gowenrw/future_badge/art/AI_to_DXF.JPG

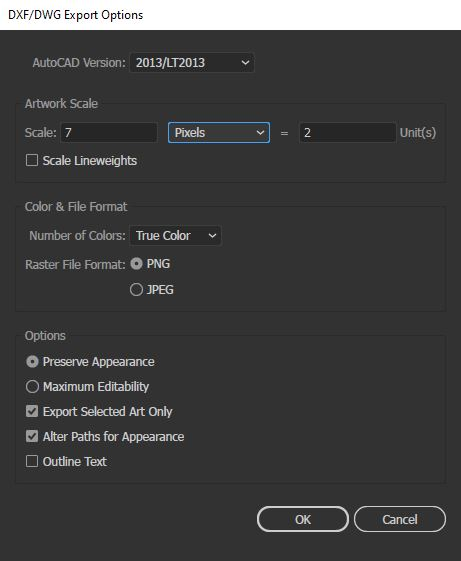
art/AI_to_DXF.JPG
