gowenrw/future_badge/art/haveadrinkonme.jpg

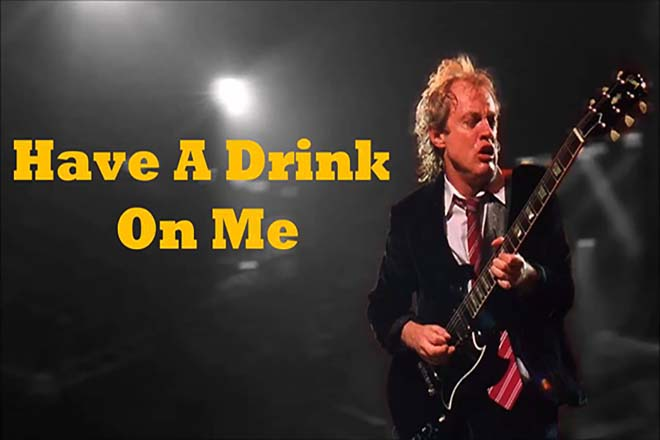
art/haveadrinkonme.jpg
