gowenrw/future_badge/art/inspiration/book_blowing_away.jpg

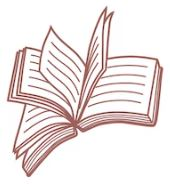
art/inspiration/book_blowing_away.jpg
