gowenrw/future_badge/art/inspiration/book_opening.jpg

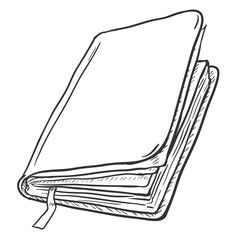
art/inspiration/book_opening.jpg
