gowenrw/future_badge/art/inspiration/bttf_back1.jpg

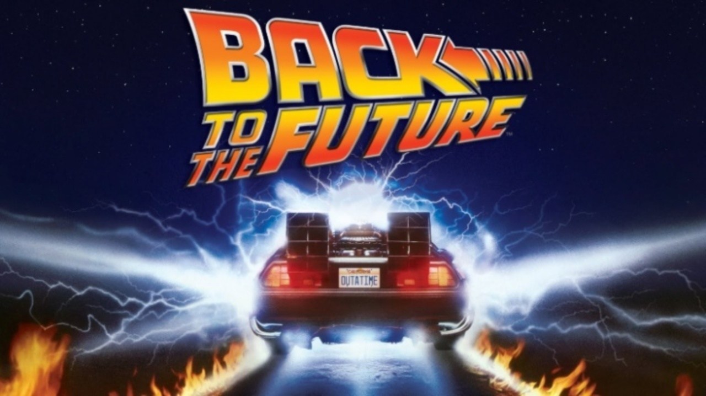
art/inspiration/bttf_back1.jpg
