gowenrw/future_badge/art/inspiration/bttf_back2.jpg

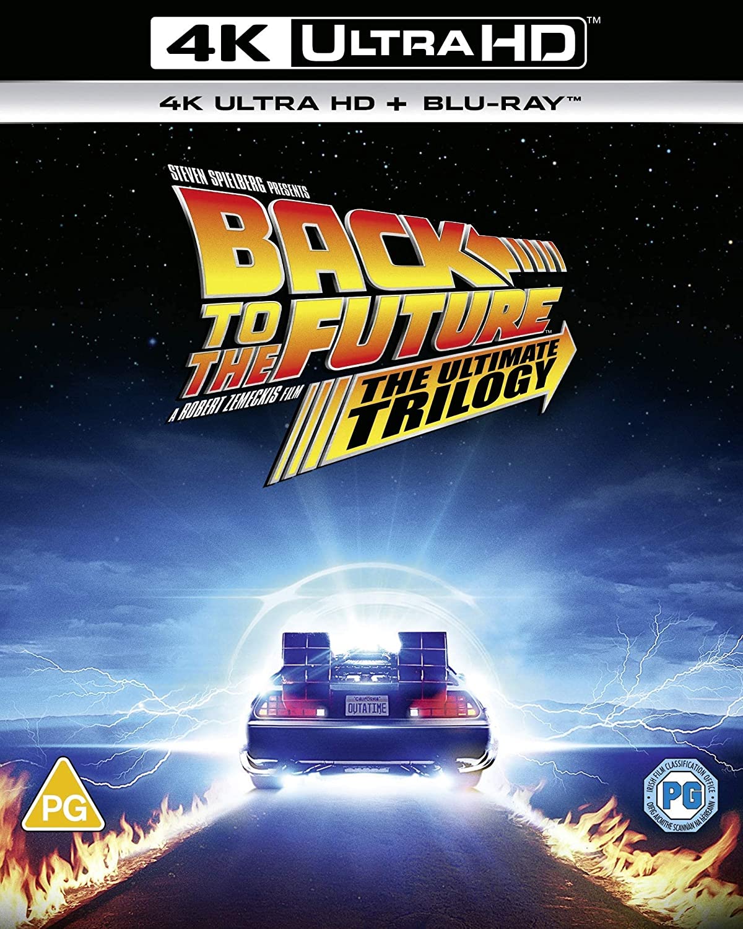
art/inspiration/bttf_back2.jpg
