gowenrw/future_badge/art/inspiration/bttf_side1.jpg

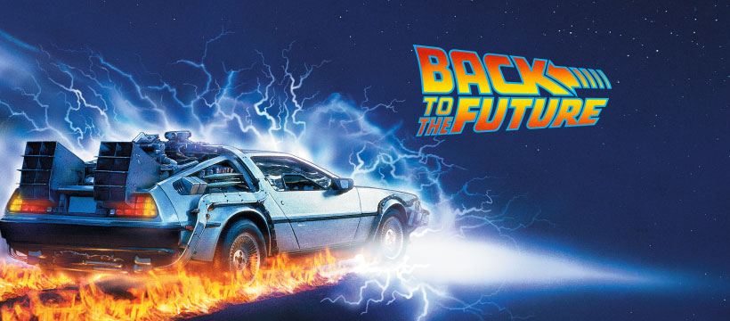
art/inspiration/bttf_side1.jpg
