gowenrw/future_badge/art/inspiration/clock_tower_1.jpg

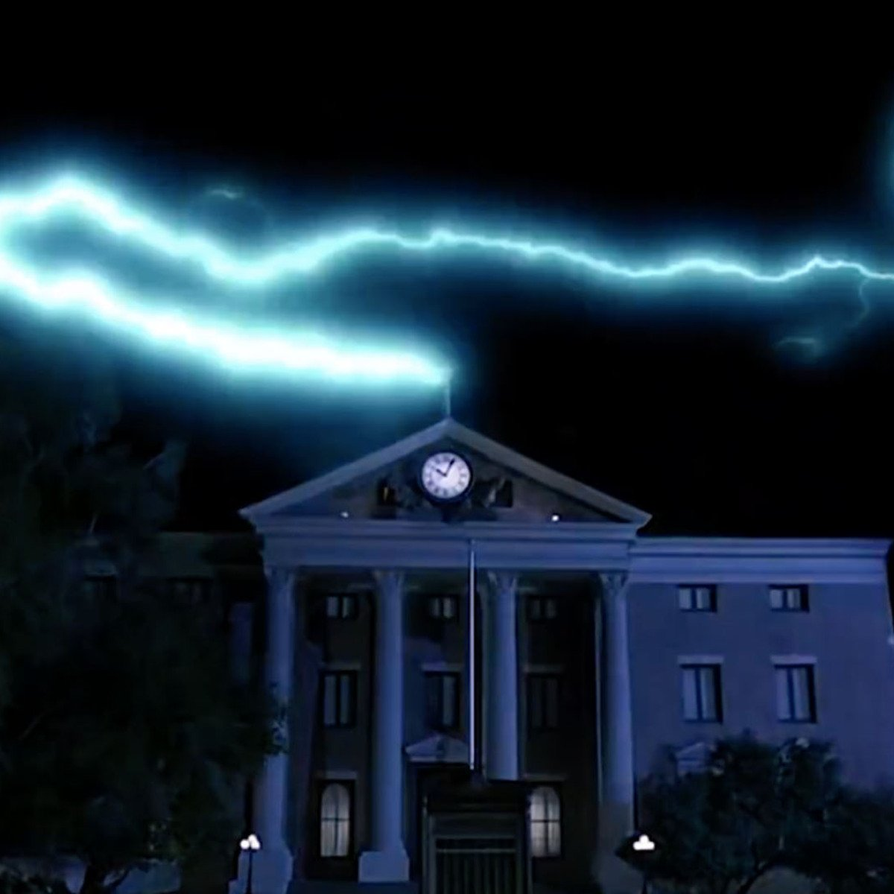
art/inspiration/clock_tower_1.jpg
