gowenrw/future_badge/art/inspiration/Doc-Shock.jpg

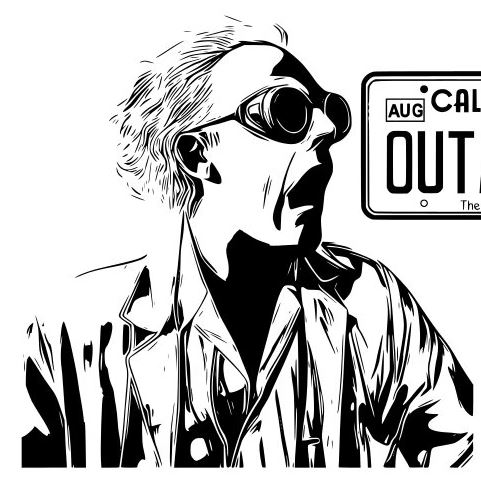
art/inspiration/Doc-Shock.jpg
