gowenrw/future_badge/art/inspiration/flux_cap.jpg

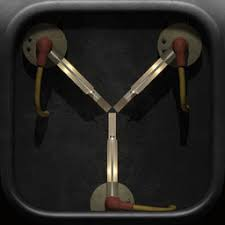
art/inspiration/flux_cap.jpg
