gowenrw/future_badge/art/inspiration/sports_almanac.jpg

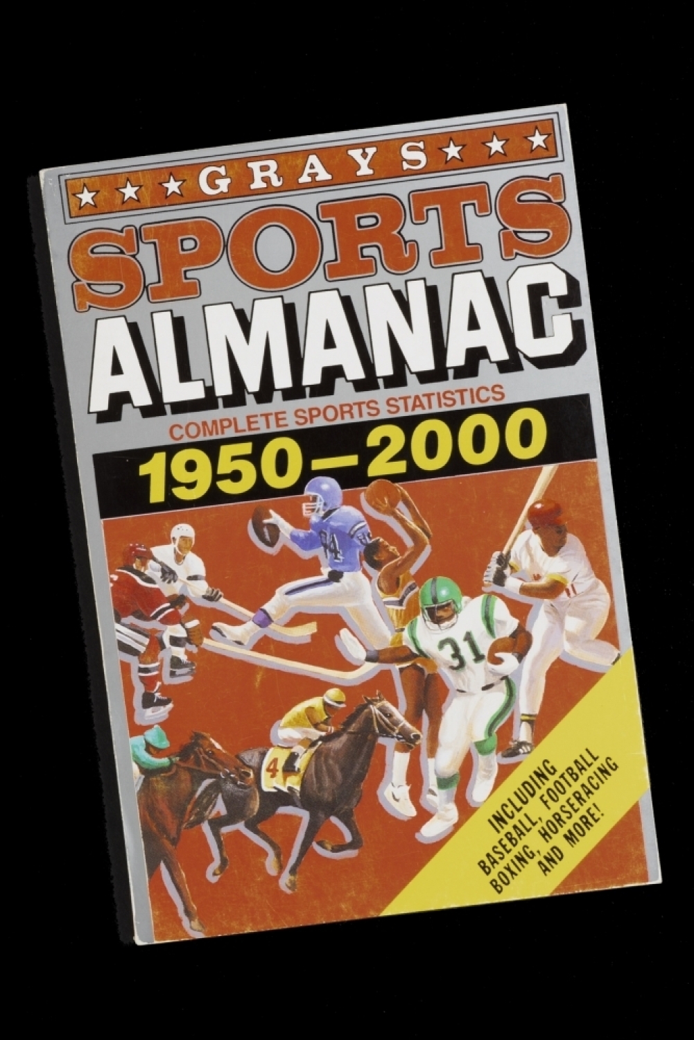
art/inspiration/sports_almanac.jpg
