gowenrw/future_badge/art/lanyard/Proof.png

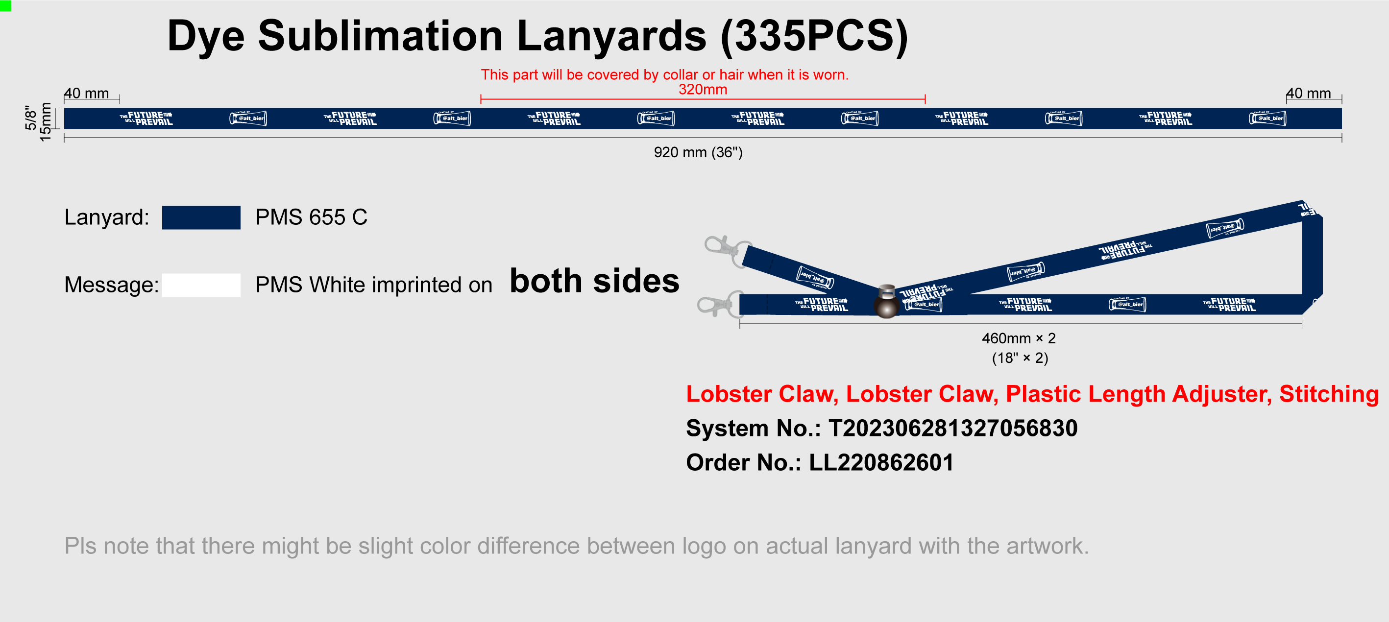
art/lanyard/Proof.png
