gowenrw/future_badge/art/prototype_pcb_full_back.jpg

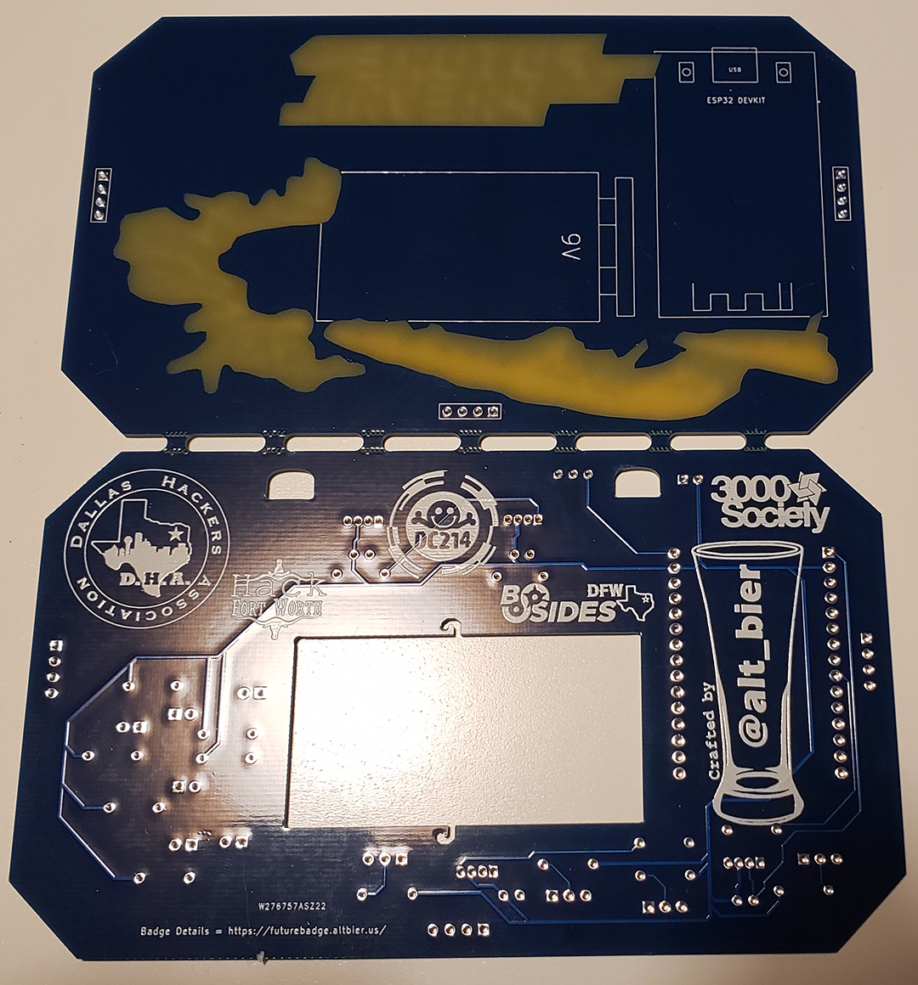
art/prototype_pcb_full_back.jpg
