gowenrw/future_badge/art/prototype_pcb_full_front.jpg

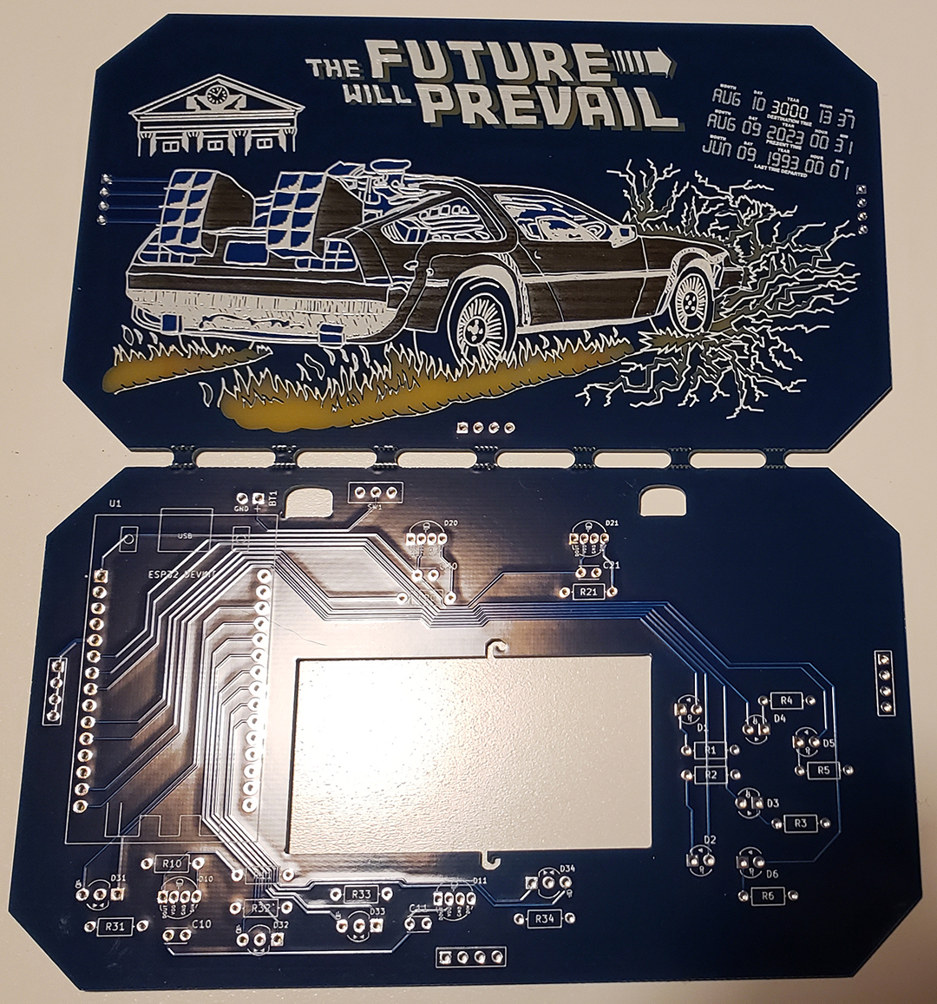
art/prototype_pcb_full_front.jpg
