gowenrw/future_badge/art/prototype_pcb_lit_up.jpg

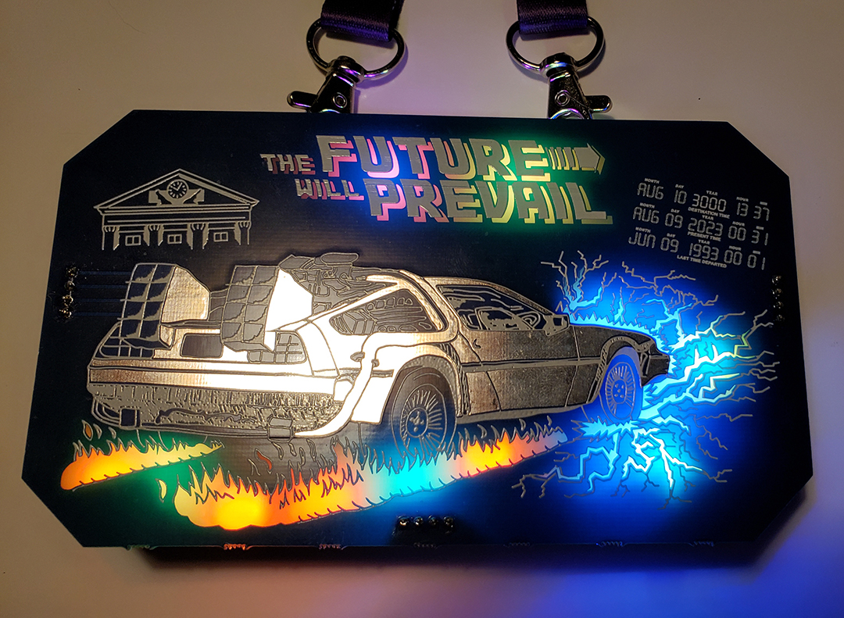
art/prototype_pcb_lit_up.jpg
