gowenrw/future_badge/art/prototype_pcb_lit_up_side_view.jpg

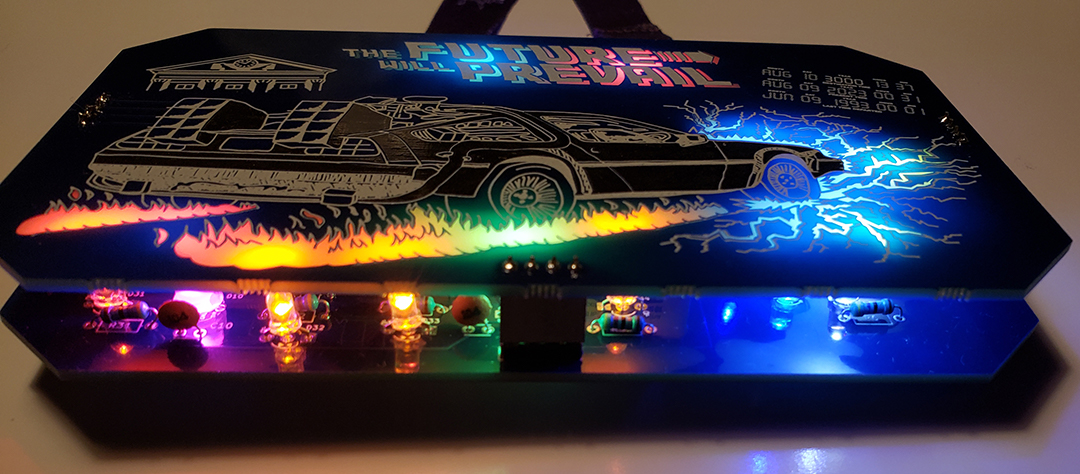
art/prototype_pcb_lit_up_side_view.jpg
