gowenrw/future_badge/art/sticker/Proof_R200018173_StickerMule.png

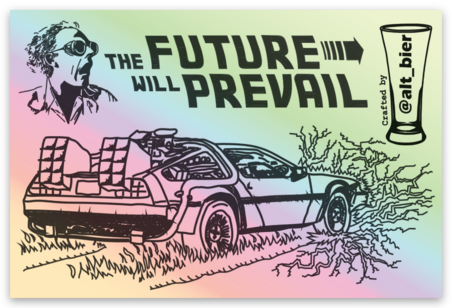
art/sticker/Proof_R200018173_StickerMule.png
