gowenrw/future_badge/docs/images/2Capture.JPG

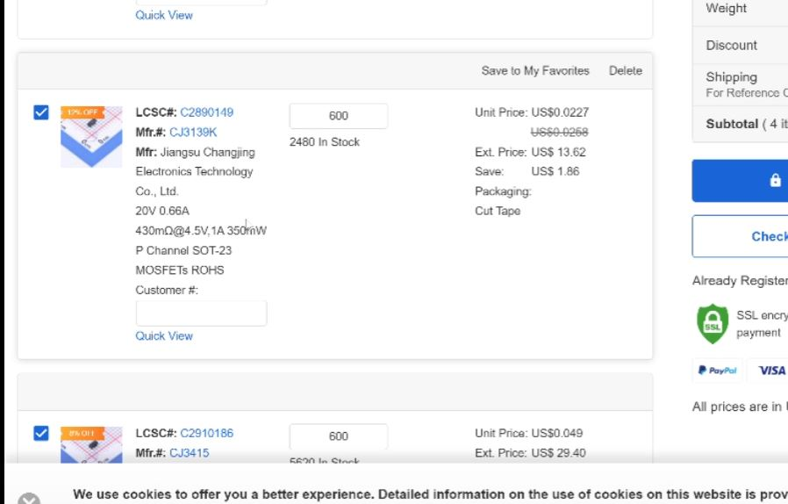
docs/images/2Capture.JPG
