gowenrw/future_badge/docs/images/ESP32-GPIO-Pins-that-are-Safe-to-Use.png

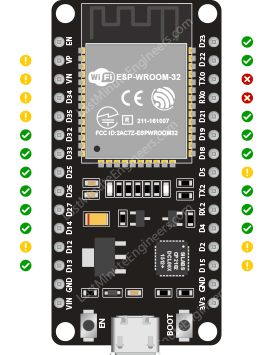
docs/images/ESP32-GPIO-Pins-that-are-Safe-to-Use.png
