gowenrw/future_badge/docs/images/prototype/20230615_201724.jpg

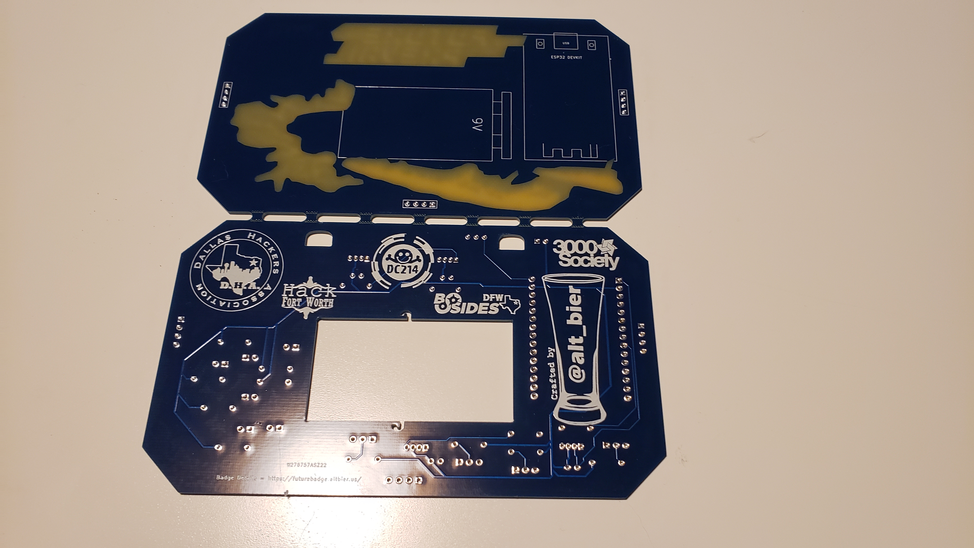
docs/images/prototype/20230615_201724.jpg
