gowenrw/future_badge/docs/images/prototype/20230615_201829.jpg

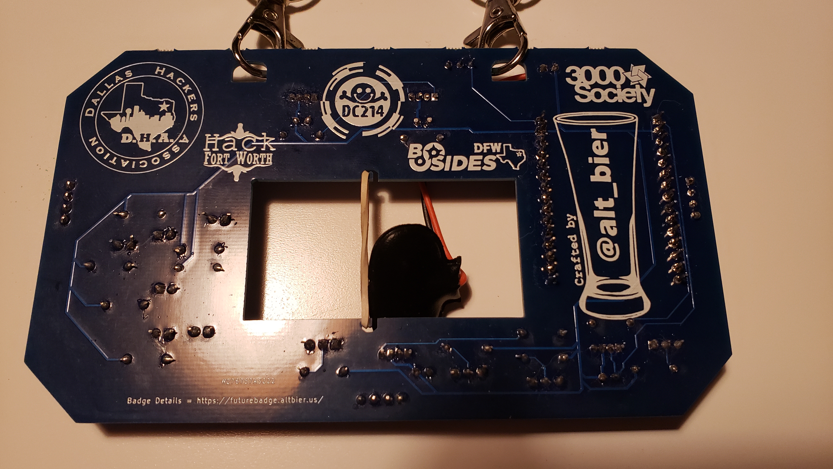
docs/images/prototype/20230615_201829.jpg
