gowenrw/future_badge/docs/images/prototype/20230615_201941.jpg

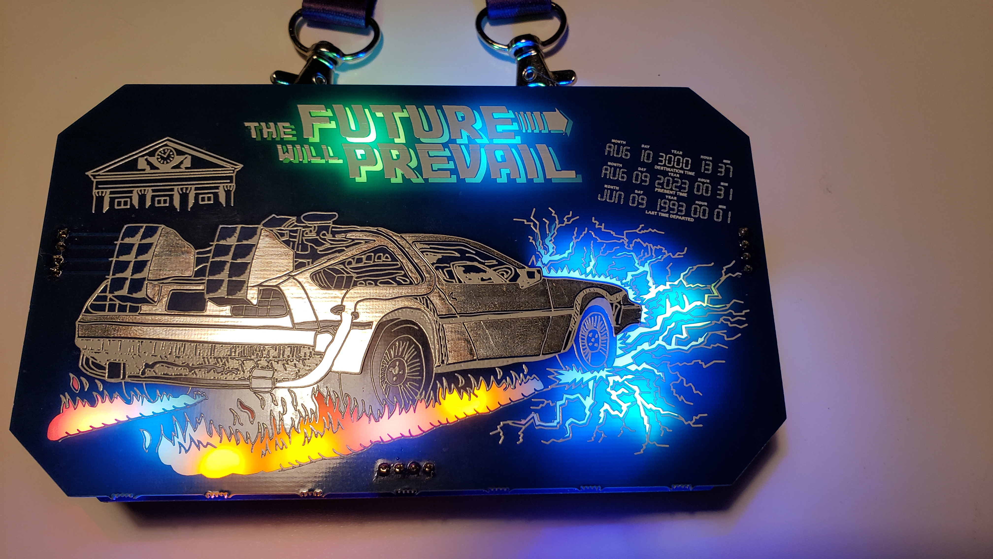
docs/images/prototype/20230615_201941.jpg
