gowenrw/future_badge/docs/images/prototype/20230615_202005.jpg

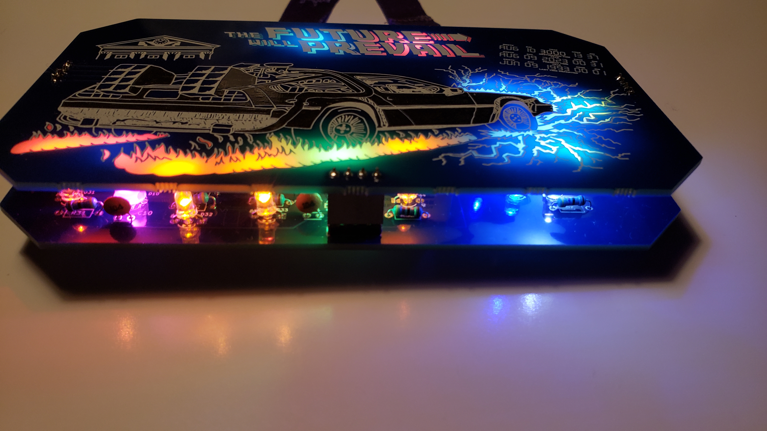
docs/images/prototype/20230615_202005.jpg
