gowenrw/future_badge/docs/images/prototype/20230705_084911.jpg

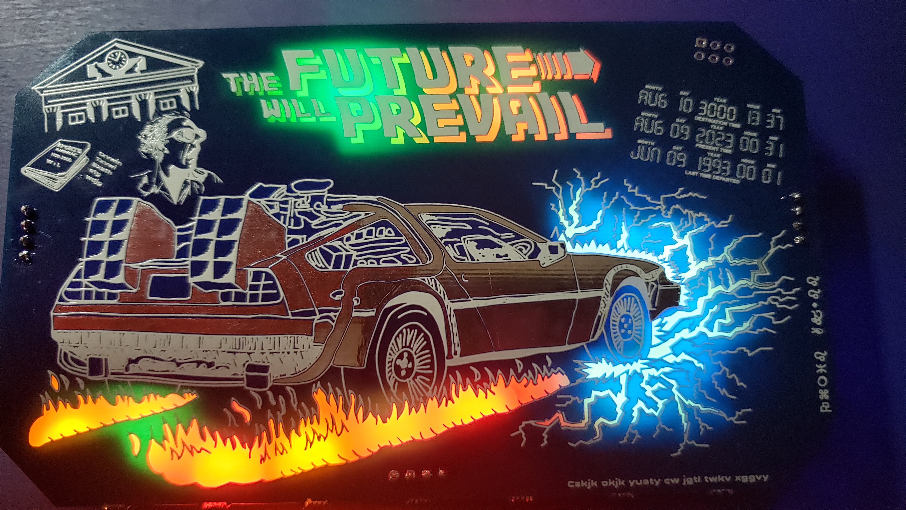
docs/images/prototype/20230705_084911.jpg
