gowenrw/future_badge/docs/images/prototype/20230705_084914.jpg

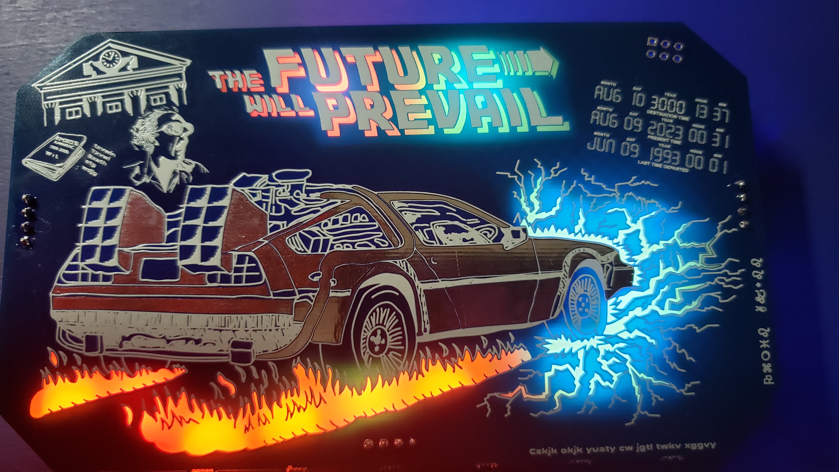
docs/images/prototype/20230705_084914.jpg
