gowenrw/future_badge/docs/images/prototype/20230705_085853.jpg

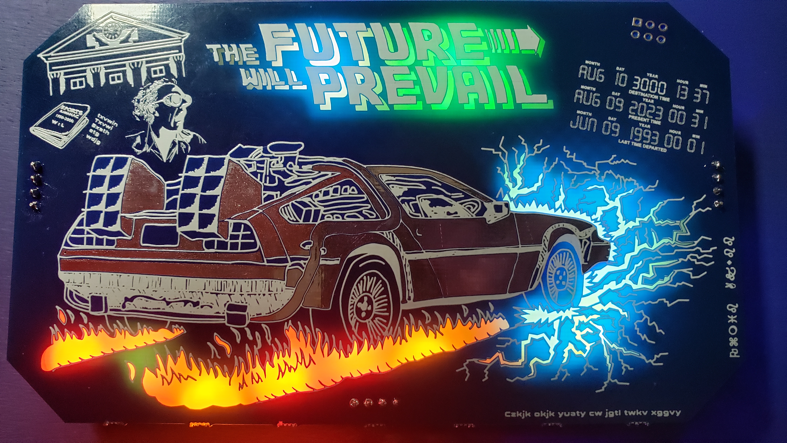
docs/images/prototype/20230705_085853.jpg
