gowenrw/future_badge/art/future_badge_art-2-backmask-lightning-7-2.dxf

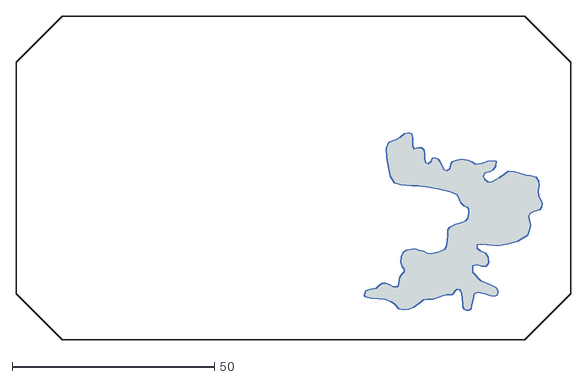
[picture p60: CAD file, 2023-06-05]
art/future_badge_art-2-backmask-lightning-7-2.dxf
137.1 x 80.0
