gowenrw/future_badge/eda/future_badge/3d_models/PinSocket_1x04_P2.54mm_Vertical.step

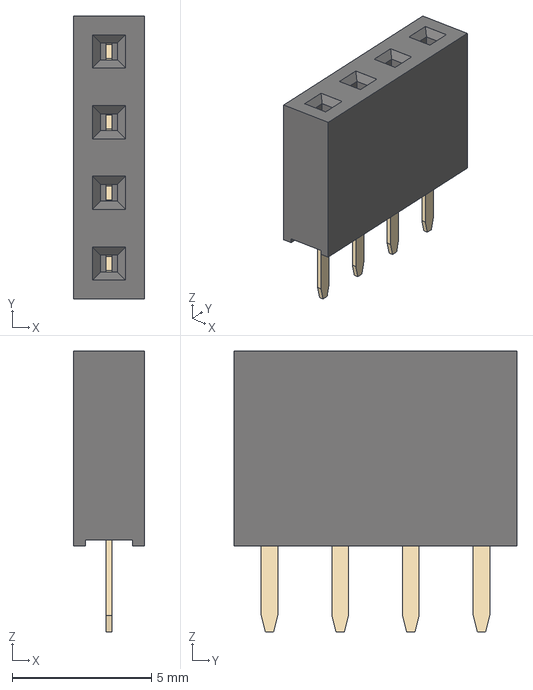
[picture p61: CAD file, 2023-06-05]
eda/future_badge/3d_models/PinSocket_1x04_P2.54mm_Vertical.step
2.54 x 10.2 x 10.1 mm
