gowenrw/future_badge/eda/future_badge/3d_models/PinSocket_1x20_P2.54mm_Vertical.step

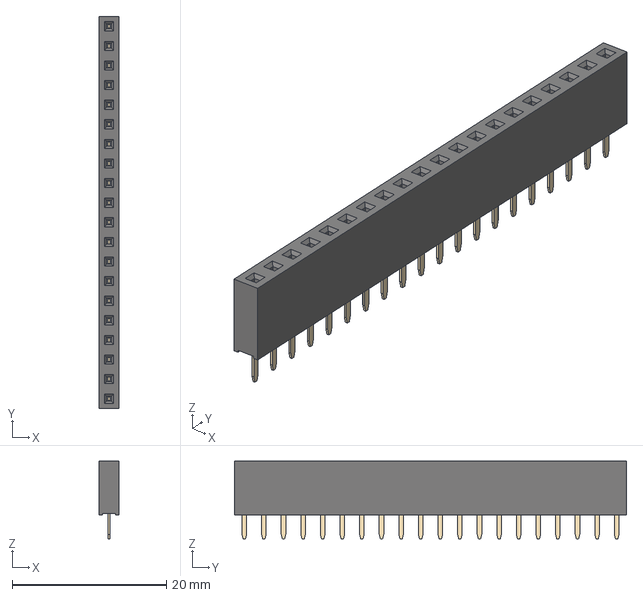
[picture p69: CAD file, 2023-06-05]
eda/future_badge/3d_models/PinSocket_1x20_P2.54mm_Vertical.step
2.54 x 50.8 x 10.1 mm
