gowenrw/future_badge/art/future_badge_art-2-frontsilk-title-txt-7-2.dxf

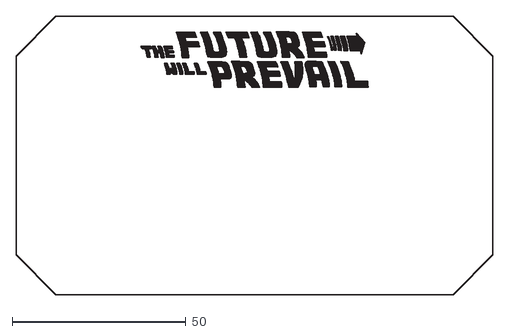
[picture p70: CAD file, 2023-06-03]
art/future_badge_art-2-frontsilk-title-txt-7-2.dxf
137.1 x 80.0
