gowenrw/future_badge/art/future_badge_art-2-frontsilk-notxt-7-2.dxf

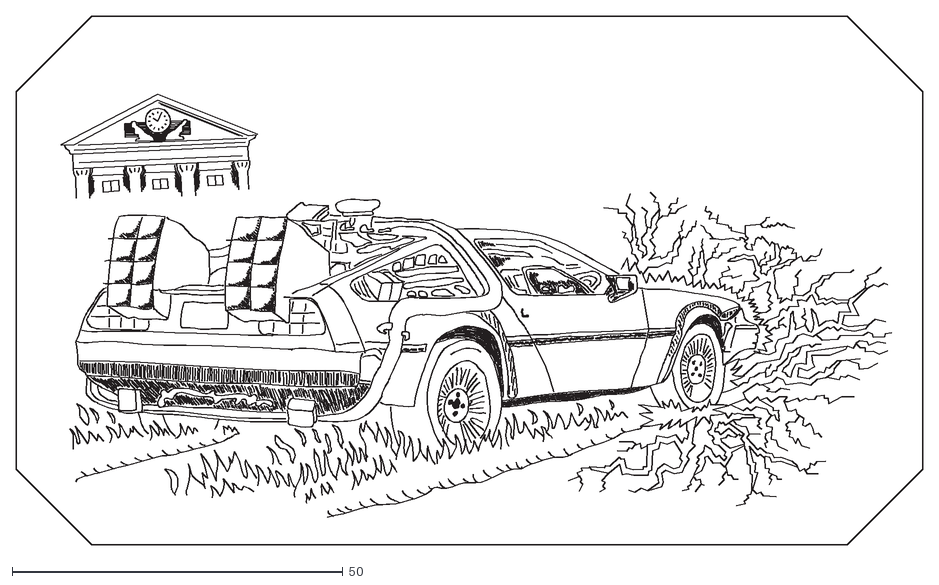
[picture p72: CAD file, 2023-06-03]
art/future_badge_art-2-frontsilk-notxt-7-2.dxf
137.1 x 80.0
