gowenrw/future_badge/art/future_badge_art-2-edgecuts-7-2.dxf

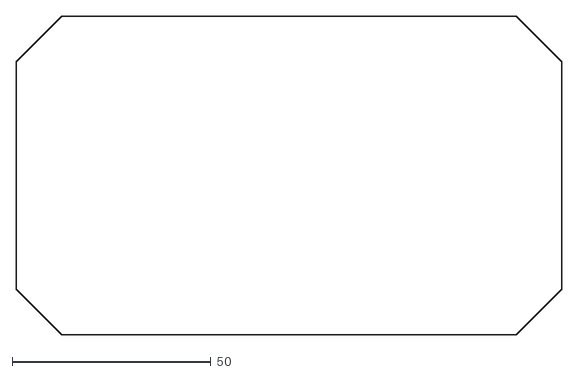
[picture p76: CAD file, 2023-06-03]
art/future_badge_art-2-edgecuts-7-2.dxf
137.1 x 80.0
