gowenrw/future_badge/eda/future_badge/3d_models/PinSocket_1x03_P2.54mm_Horizontal.step

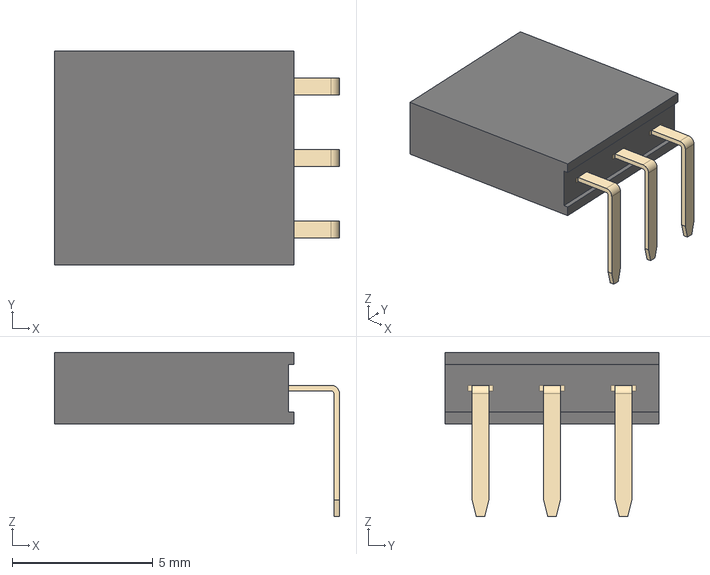
[picture p77: CAD file, 2023-06-05]
eda/future_badge/3d_models/PinSocket_1x03_P2.54mm_Horizontal.step
10.1 x 7.62 x 5.84 mm
