gowenrw/future_badge/eda/future_badge/3d_models/PinSocket_1x04_P2.54mm_Horizontal.step

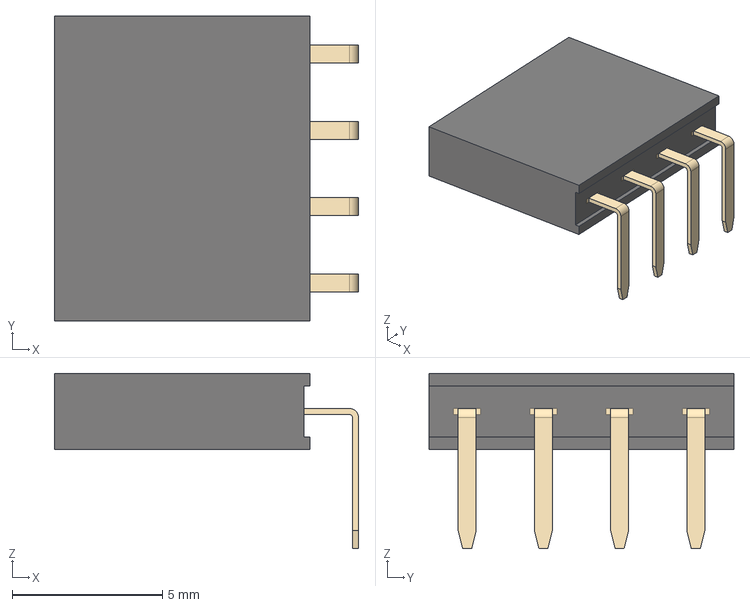
[picture p79: CAD file, 2023-06-05]
eda/future_badge/3d_models/PinSocket_1x04_P2.54mm_Horizontal.step
10.1 x 10.2 x 5.84 mm
