gowenrw/future_badge/eda/future_badge/3d_models/LED_D5.0mm-4_RGB_Neo.step

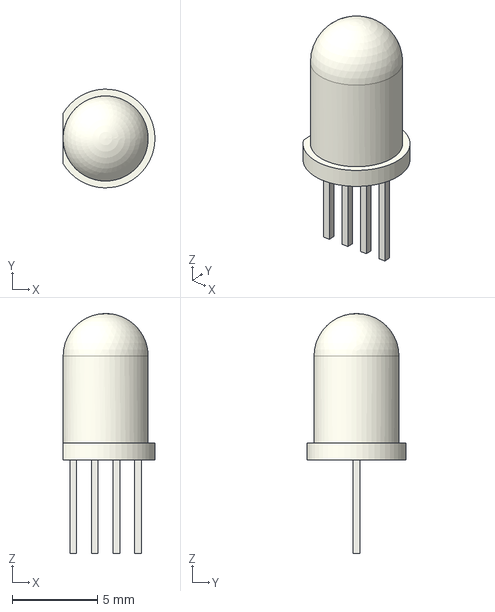
[picture p81: CAD file, 2023-04-15]
eda/future_badge/3d_models/LED_D5.0mm-4_RGB_Neo.step
5.40 x 5.79 x 14.1 mm
