gowenrw/future_badge/eda/future_badge/3d_models/USB_Micro-B_Molex_47346-0001.step

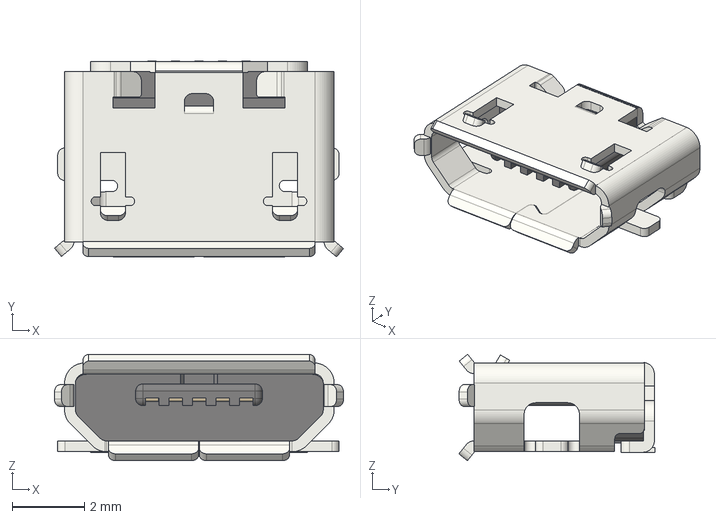
[picture p82: CAD file, 2023-04-15]
eda/future_badge/3d_models/USB_Micro-B_Molex_47346-0001.step
7.98 x 5.42 x 2.94 mm
