gowenrw/future_badge/eda/future_badge/3d_models/CP_Radial_D6.3mm_P2.50mm.step

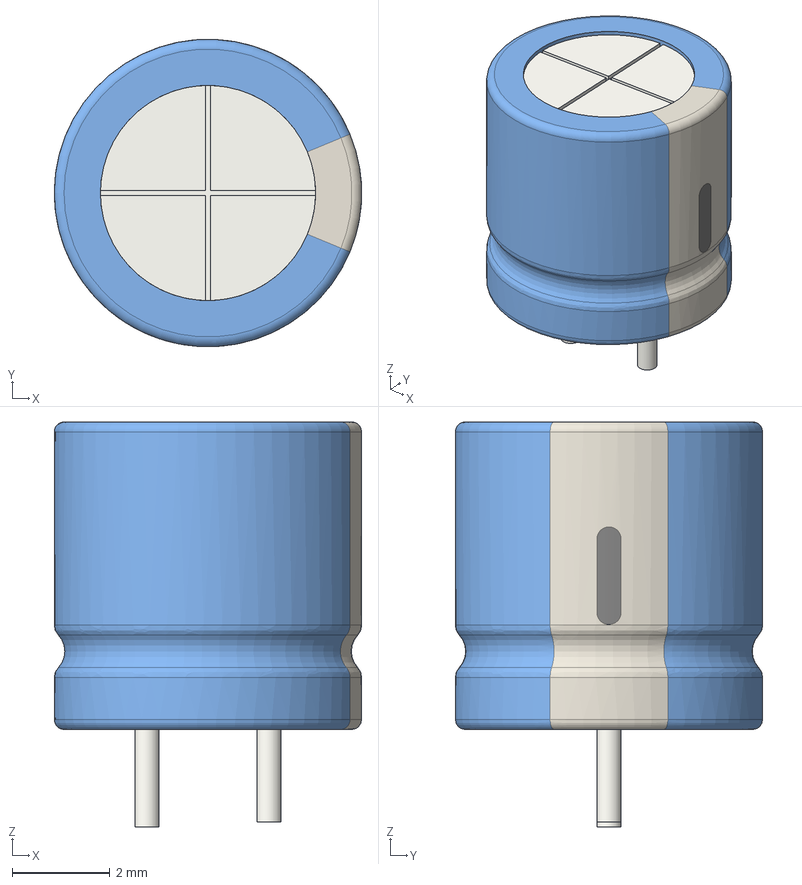
[picture p83: CAD file, 2023-04-15]
eda/future_badge/3d_models/CP_Radial_D6.3mm_P2.50mm.step
6.30 x 6.30 x 8.30 mm
