gowenrw/future_badge/eda/future_badge/3d_models/PinHeader_1x06_P2.54mm_Horizontal.step

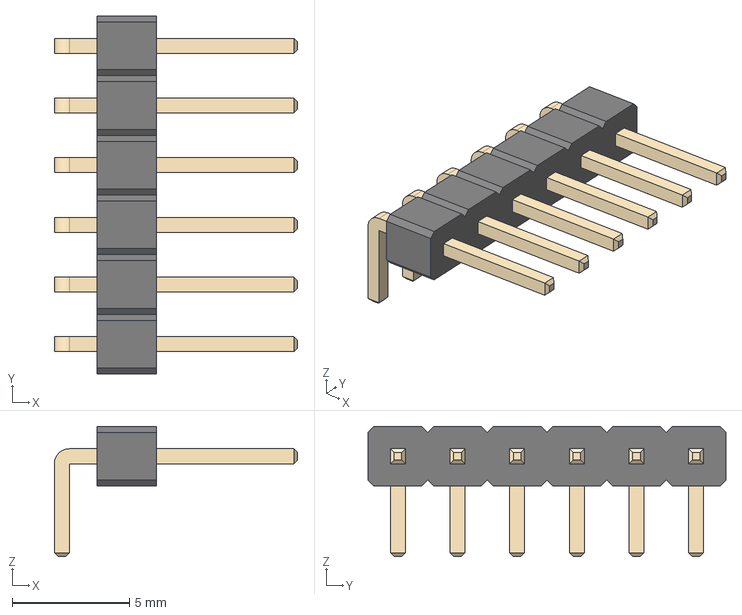
[picture p89: CAD file, 2023-04-15]
eda/future_badge/3d_models/PinHeader_1x06_P2.54mm_Horizontal.step
10.4 x 15.2 x 5.54 mm
