gowenrw/future_badge/eda/future_badge/3d_models/PinSocket_1x01_P2.54mm_Vertical.step

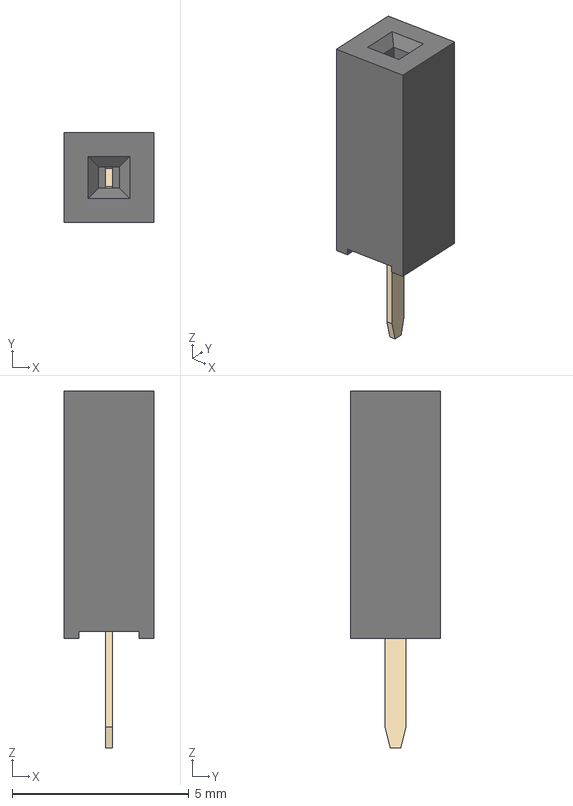
[picture p92: CAD file, 2023-04-15]
eda/future_badge/3d_models/PinSocket_1x01_P2.54mm_Vertical.step
2.54 x 2.54 x 10.1 mm
