gowenrw/future_badge/eda/future_badge/3d_models/PinSocket_1x08_P2.54mm_Horizontal.step

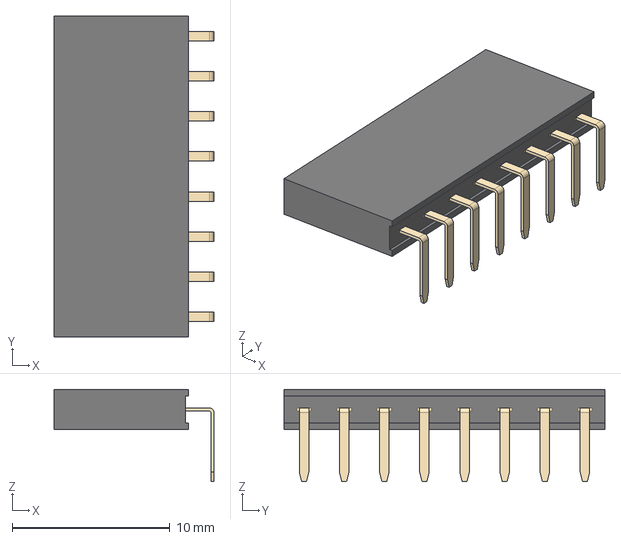
[picture p93: CAD file, 2023-04-15]
eda/future_badge/3d_models/PinSocket_1x08_P2.54mm_Horizontal.step
10.1 x 20.3 x 5.84 mm
