gowenrw/future_badge/eda/future_badge/3d_models/Battery_Holder_3xAAA_Simple.step

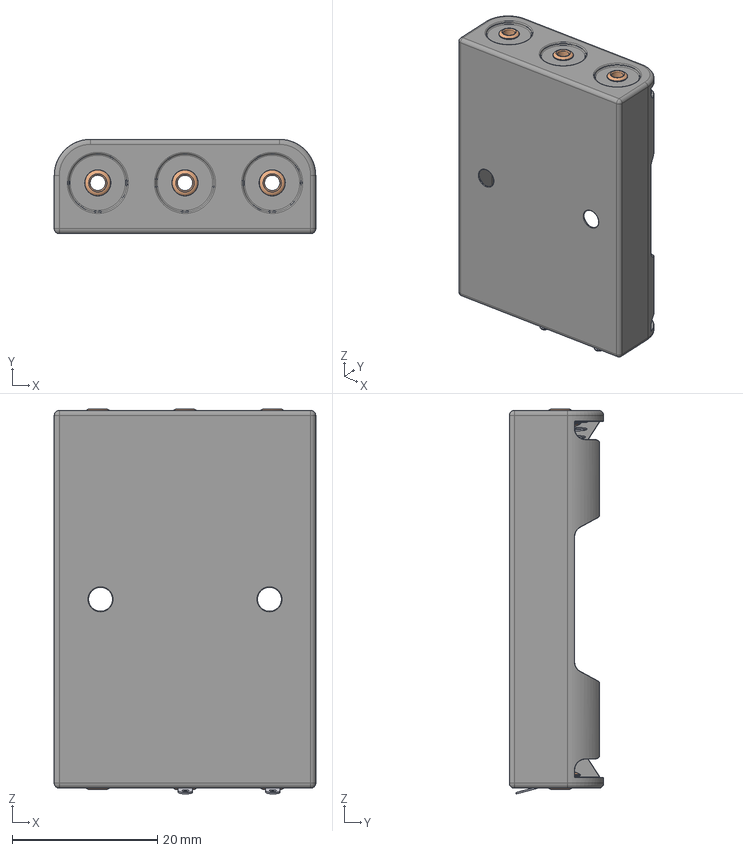
[picture p94: CAD file, 2023-04-15]
eda/future_badge/3d_models/Battery_Holder_3xAAA_Simple.step
36.0 x 13.0 x 53.0 mm
