gowenrw/future_badge/eda/future_badge/3d_models/LED_0805_2012Metric_Castellated.step

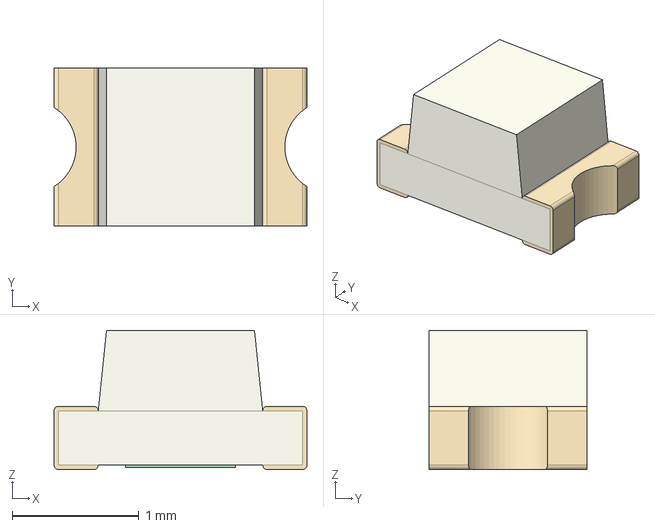
[picture p97: CAD file, 2023-04-15]
eda/future_badge/3d_models/LED_0805_2012Metric_Castellated.step
2.00 x 1.25 x 1.10 mm
