gowenrw/future_badge/eda/future_badge/3d_models/LED_D8.0mm.step

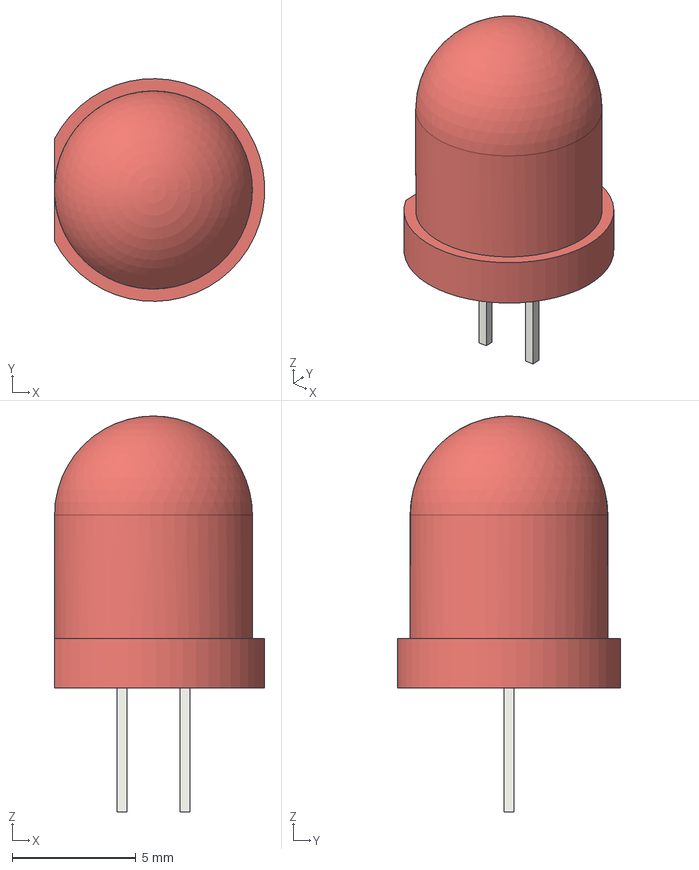
[picture p98: CAD file, 2023-04-15]
eda/future_badge/3d_models/LED_D8.0mm.step
8.49 x 9.00 x 16.0 mm
