gowenrw/future_badge/eda/future_badge/3d_models/PinHeader_1x04_P2.54mm_Vertical.step

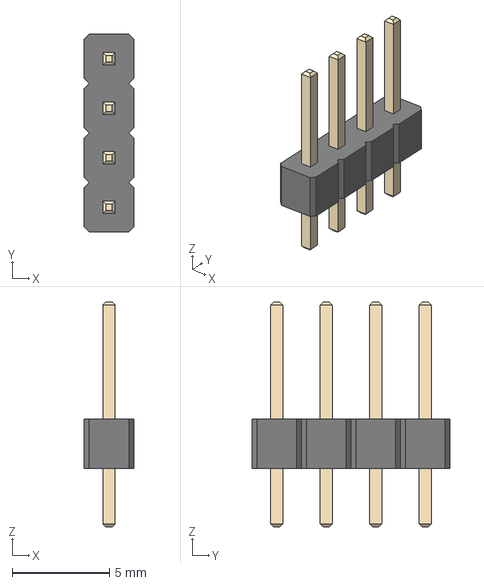
[picture p100: CAD file, 2023-04-15]
eda/future_badge/3d_models/PinHeader_1x04_P2.54mm_Vertical.step
2.54 x 10.2 x 11.5 mm
