gowenrw/future_badge/eda/future_badge/3d_models/LED_D5.0mm.step

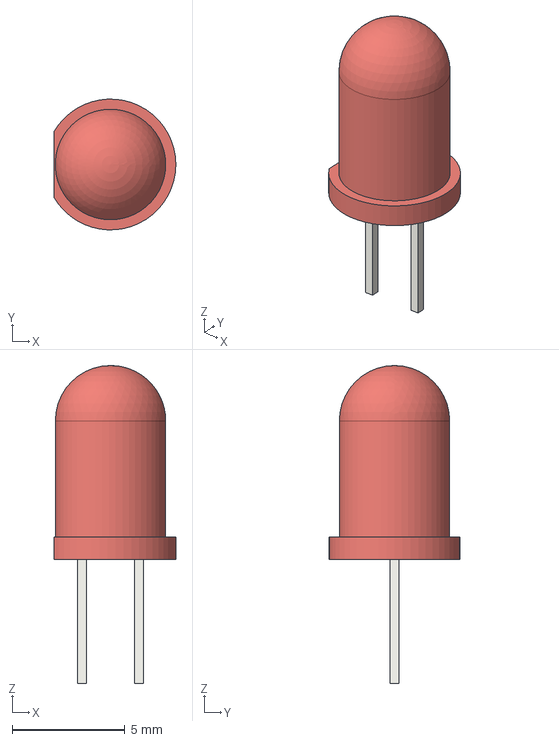
[picture p101: CAD file, 2023-04-15]
eda/future_badge/3d_models/LED_D5.0mm.step
5.40 x 5.79 x 14.1 mm
