gowenrw/future_badge/eda/future_badge/3d_models/BatteryHolder_2466_1xAAA.step

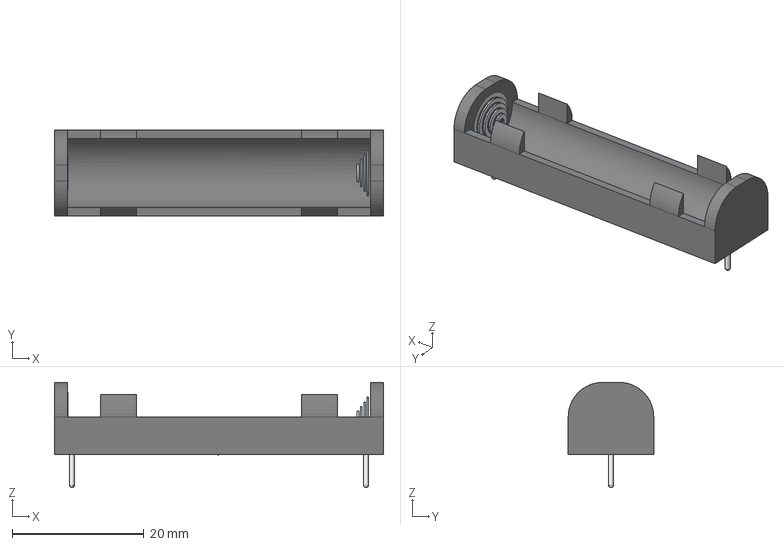
[picture p102: CAD file, 2023-04-15]
eda/future_badge/3d_models/BatteryHolder_2466_1xAAA.step
50.0 x 13.0 x 16.0 mm
