gowenrw/future_badge/eda/future_badge/3d_models/RJ45_Amphenol_RJHSE538X.step

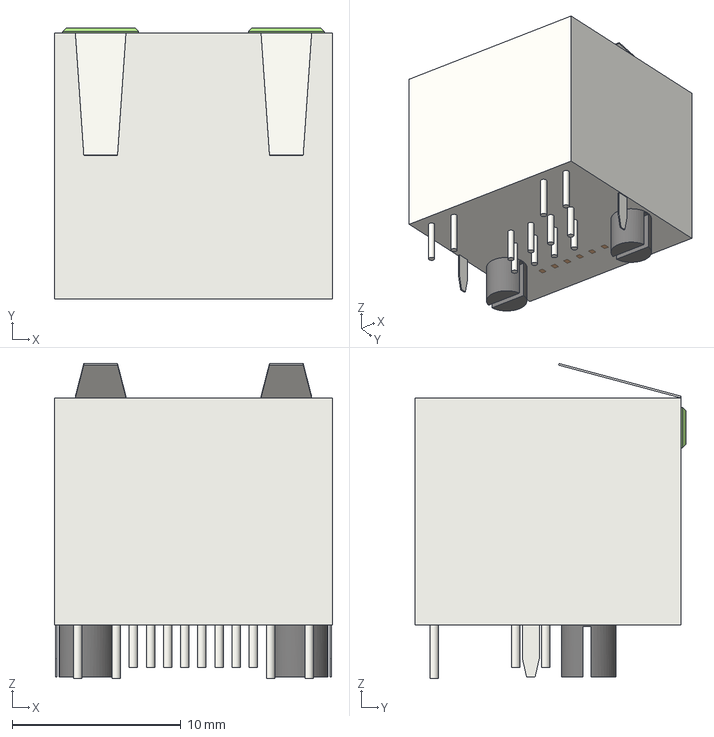
[picture p103: CAD file, 2023-04-15]
eda/future_badge/3d_models/RJ45_Amphenol_RJHSE538X.step
16.5 x 16.1 x 18.7 mm
