gowenrw/future_badge/eda/future_badge/3d_models/R_0805_2012Metric.step

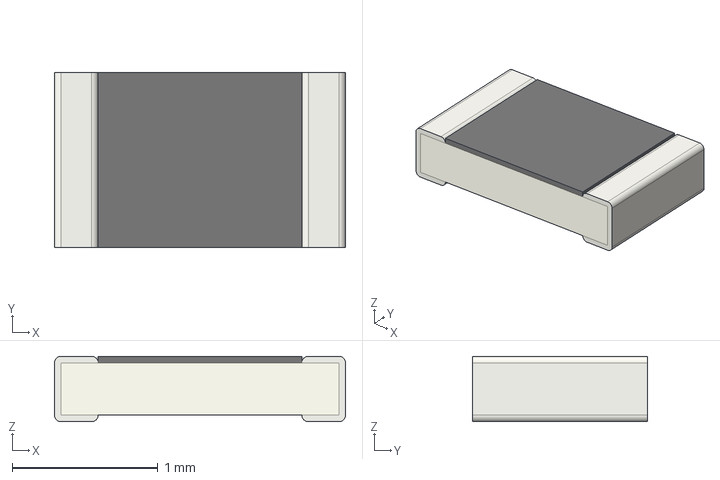
[picture p105: CAD file, 2023-04-15]
eda/future_badge/3d_models/R_0805_2012Metric.step
2.00 x 1.20 x 0.45 mm
