gowenrw/future_badge/eda/future_badge/3d_models/Battery_Holder_CR2032_BS-2-1.stp

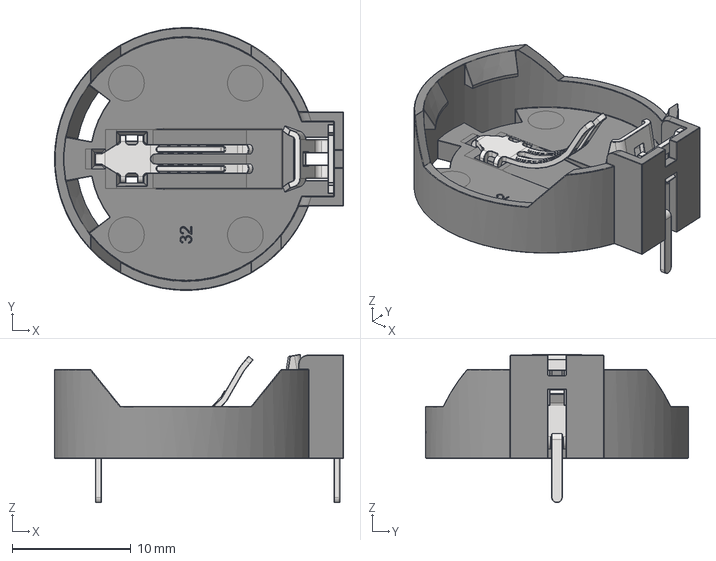
[picture p106: CAD file, 2023-04-15]
eda/future_badge/3d_models/Battery_Holder_CR2032_BS-2-1.stp
24.3 x 22.1 x 12.5 mm
