gowenrw/future_badge/eda/future_badge/3d_models/C_1206_3216Metric.step

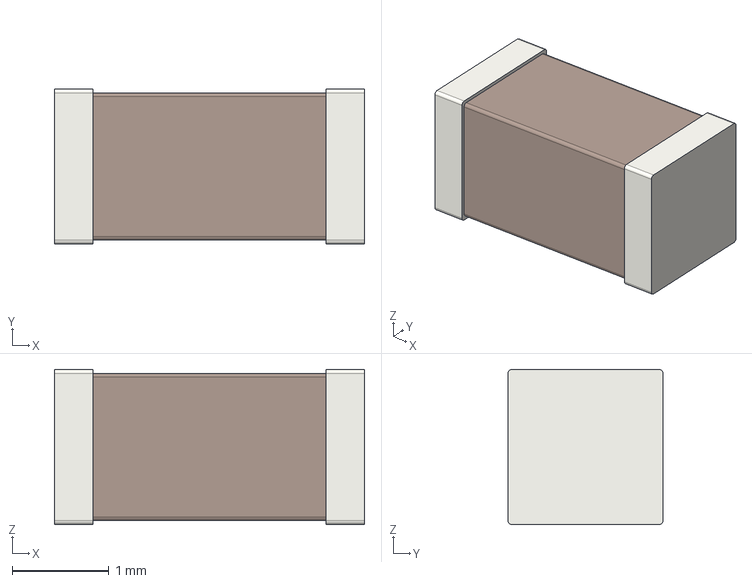
[picture p107: CAD file, 2023-04-15]
eda/future_badge/3d_models/C_1206_3216Metric.step
3.20 x 1.60 x 1.60 mm
