gowenrw/future_badge/eda/future_badge/3d_models/LED_D3.0mm-3.step

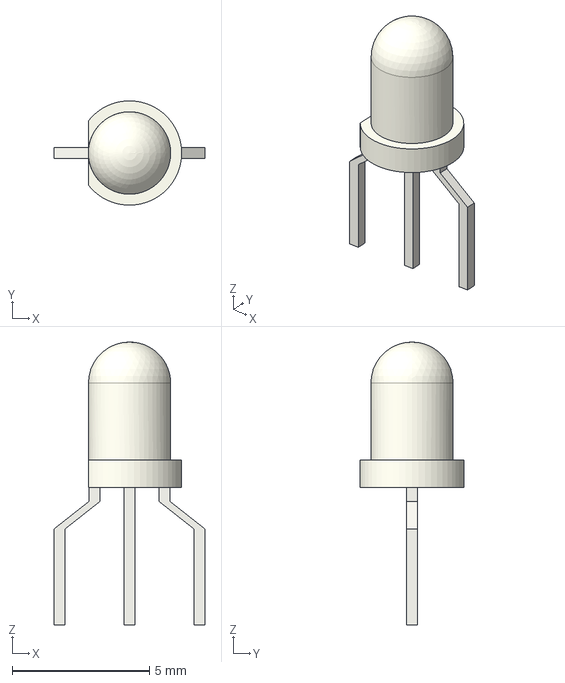
[picture p108: CAD file, 2023-04-15]
eda/future_badge/3d_models/LED_D3.0mm-3.step
5.48 x 3.80 x 10.3 mm
