gowenrw/future_badge/eda/future_badge/3d_models/R_0603_1608Metric.step

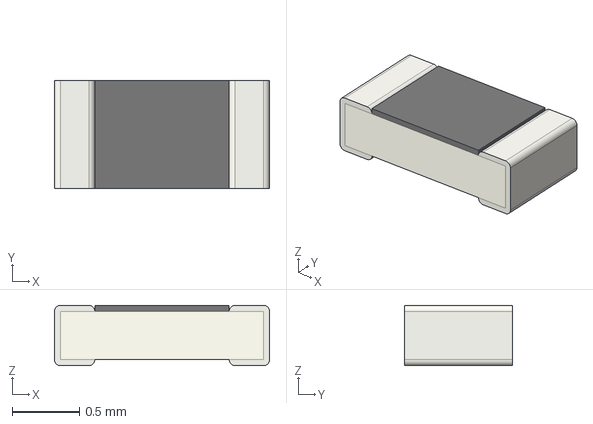
[picture p109: CAD file, 2023-04-15]
eda/future_badge/3d_models/R_0603_1608Metric.step
1.60 x 0.8 x 0.45 mm
