gowenrw/future_badge/eda/future_badge/3d_models/LED_0603_1608Metric_Castellated.step

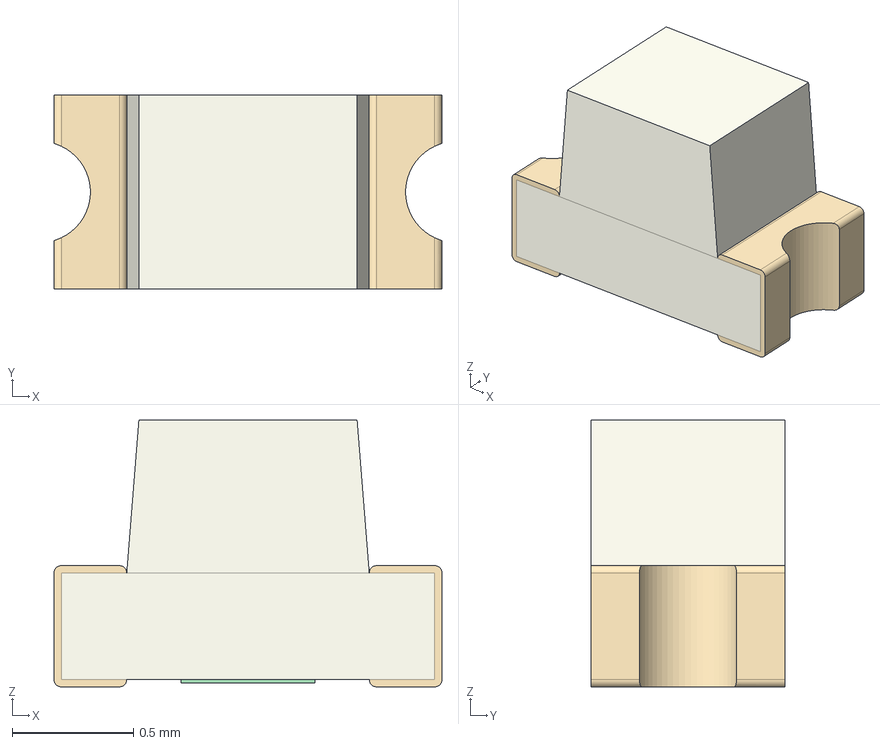
[picture p113: CAD file, 2023-04-15]
eda/future_badge/3d_models/LED_0603_1608Metric_Castellated.step
1.60 x 0.8 x 1.10 mm
