gowenrw/future_badge/eda/future_badge/3d_models/SW_SPDT_PCM12.step

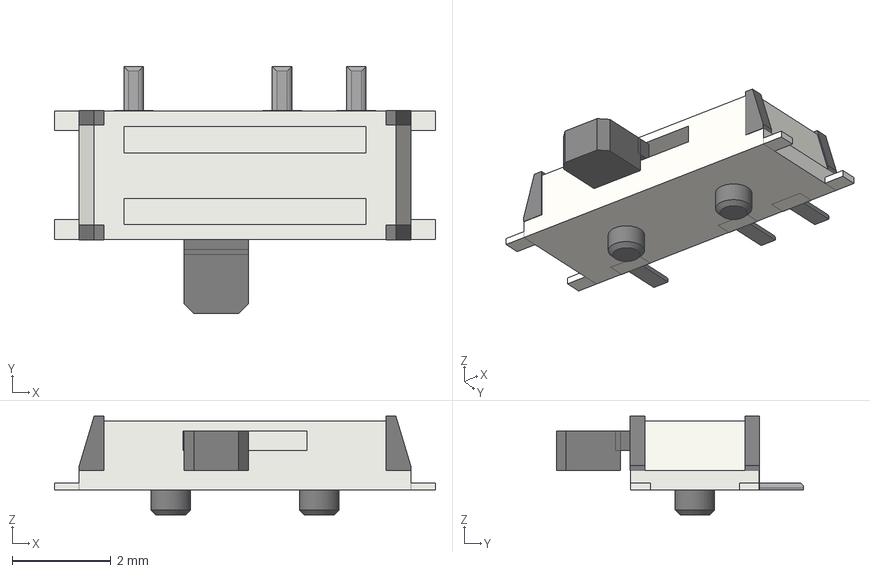
[picture p114: CAD file, 2023-04-15]
eda/future_badge/3d_models/SW_SPDT_PCM12.step
7.70 x 5.00 x 2.00 mm
