gowenrw/future_badge/eda/future_badge/3d_models/TS2306A.step

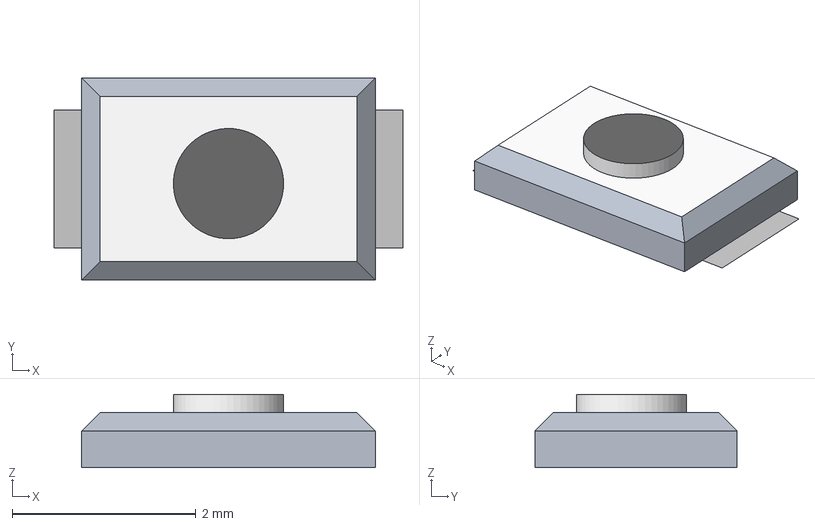
[picture p116: CAD file, 2023-04-15]
eda/future_badge/3d_models/TS2306A.step
3.80 x 2.20 x 0.8 mm
Plane
