gowenrw/future_badge/eda/future_badge/3d_models/C_0805_2012Metric.step

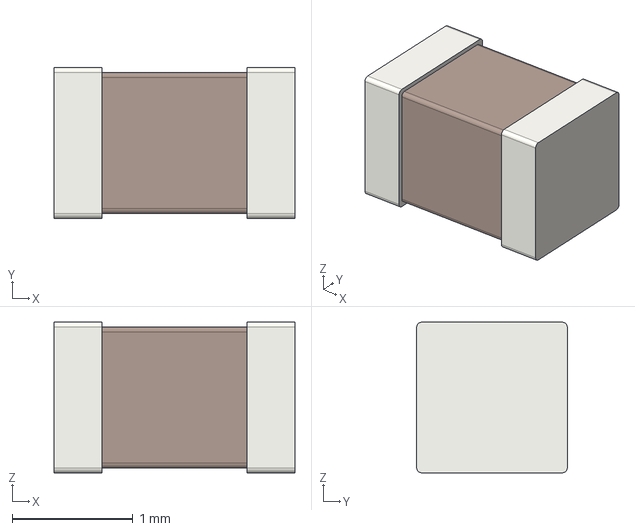
[picture p120: CAD file, 2023-04-15]
eda/future_badge/3d_models/C_0805_2012Metric.step
2.00 x 1.25 x 1.25 mm
