gowenrw/future_badge/eda/future_badge/3d_models/C_0603_1608Metric.step

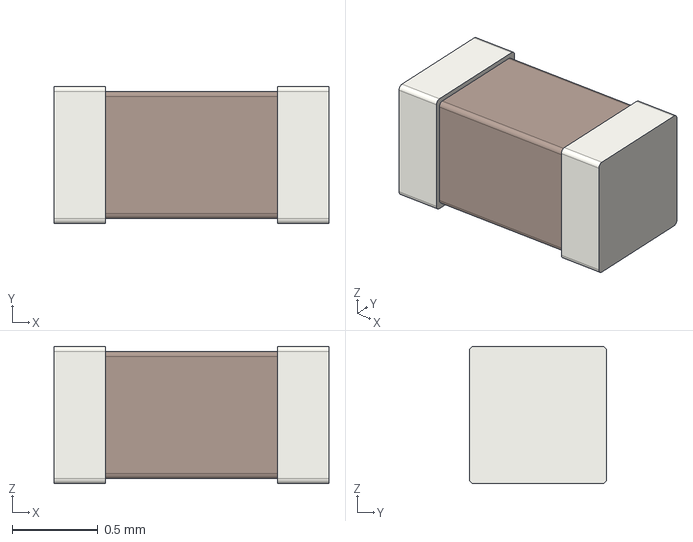
[picture p123: CAD file, 2023-04-15]
eda/future_badge/3d_models/C_0603_1608Metric.step
1.60 x 0.8 x 0.8 mm
