gowenrw/future_badge/eda/future_badge/3d_models/CP_Radial_D5.0mm_P2.00mm.step

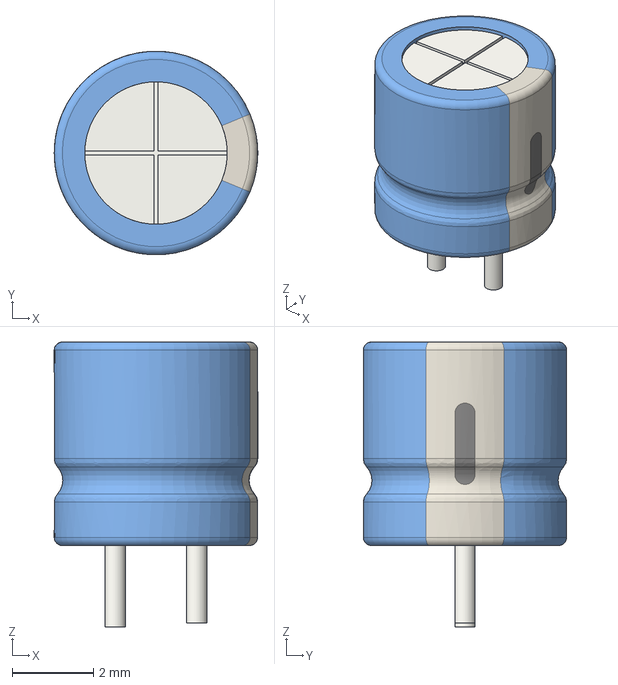
[picture p124: CAD file, 2023-04-15]
eda/future_badge/3d_models/CP_Radial_D5.0mm_P2.00mm.step
5.00 x 5.00 x 7.00 mm
