gowenrw/future_badge/eda/future_badge/3d_models/SOT-23.step

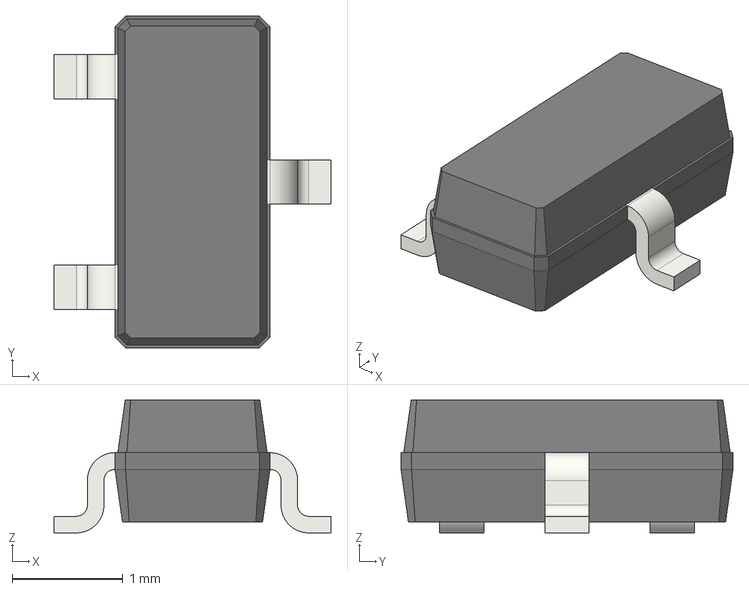
[picture p125: CAD file, 2023-04-15]
eda/future_badge/3d_models/SOT-23.step
2.50 x 3.00 x 1.20 mm
