gowenrw/future_badge/eda/future_badge/3d_models/RJ45_Amphenol_RJHSE-5080-56544.STEP

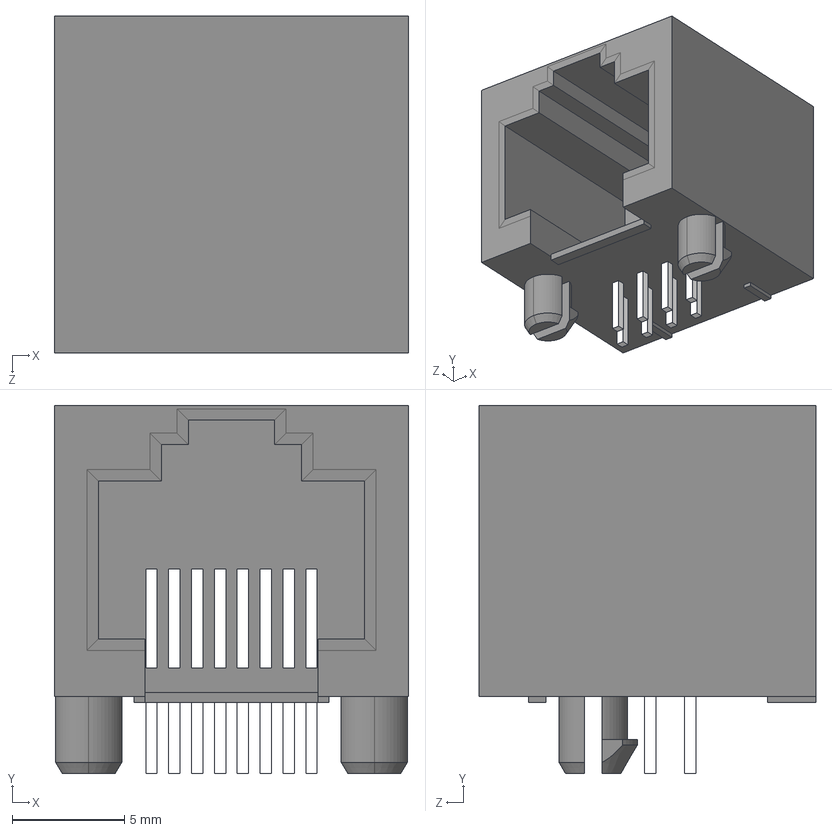
[picture p129: CAD file, 2023-04-15]
eda/future_badge/3d_models/RJ45_Amphenol_RJHSE-5080-56544.STEP
15.7 x 16.4 x 15.0 mm
