gowenrw/future_badge/eda/future_badge/3d_models/SOIC-16_3.9x9.9mm_P1.27mm.step

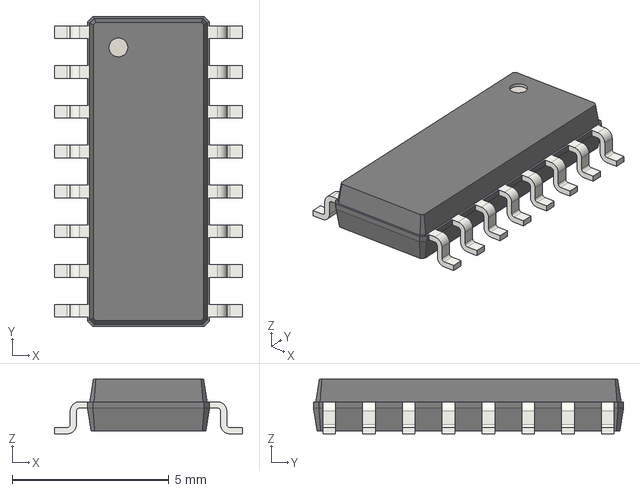
[picture p131: CAD file, 2023-04-15]
eda/future_badge/3d_models/SOIC-16_3.9x9.9mm_P1.27mm.step
6.00 x 9.90 x 1.75 mm
