gowenrw/future_badge/eda/future_badge/3d_models/LED_1206_3216Metric_Castellated.step

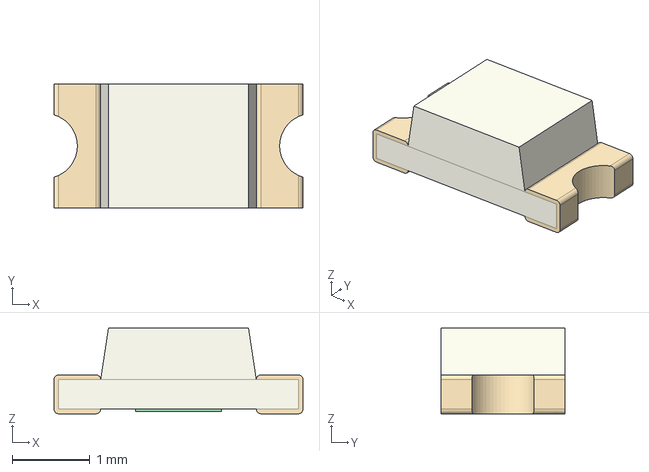
[picture p132: CAD file, 2023-04-15]
eda/future_badge/3d_models/LED_1206_3216Metric_Castellated.step
3.20 x 1.60 x 1.10 mm
