gowenrw/future_badge/eda/future_badge/3d_models/C_Rect_L4.6mm_W2.0mm_P2.50mm_MKS02_FKP02.step

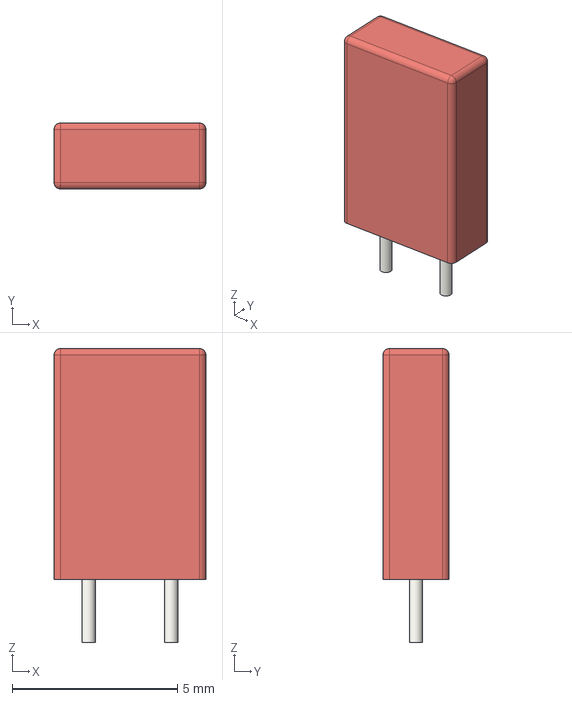
[picture p135: CAD file, 2023-04-15]
eda/future_badge/3d_models/C_Rect_L4.6mm_W2.0mm_P2.50mm_MKS02_FKP02.step
4.60 x 2.00 x 8.90 mm
