gowenrw/future_badge/eda/future_badge/3d_models/BatteryHolder_2468_2xAAA.step

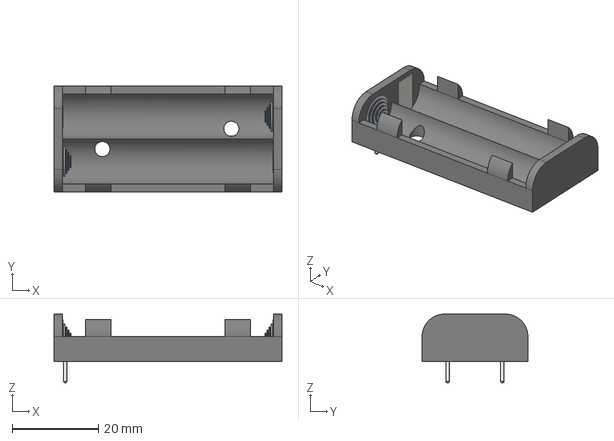
[picture p136: CAD file, 2023-04-15]
eda/future_badge/3d_models/BatteryHolder_2468_2xAAA.step
53.0 x 24.6 x 16.0 mm
