gowenrw/future_badge/eda/future_badge/3d_models/TO-92_Inline.step

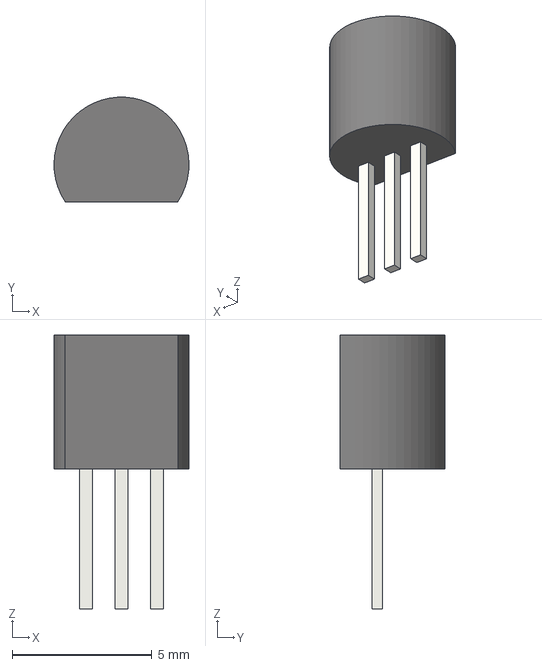
[picture p137: CAD file, 2023-04-15]
eda/future_badge/3d_models/TO-92_Inline.step
4.83 x 3.74 x 9.80 mm
