gowenrw/future_badge/eda/future_badge/3d_models/R_Axial_DIN0204_L3.6mm_D1.6mm_P5.08mm_Horizontal.step

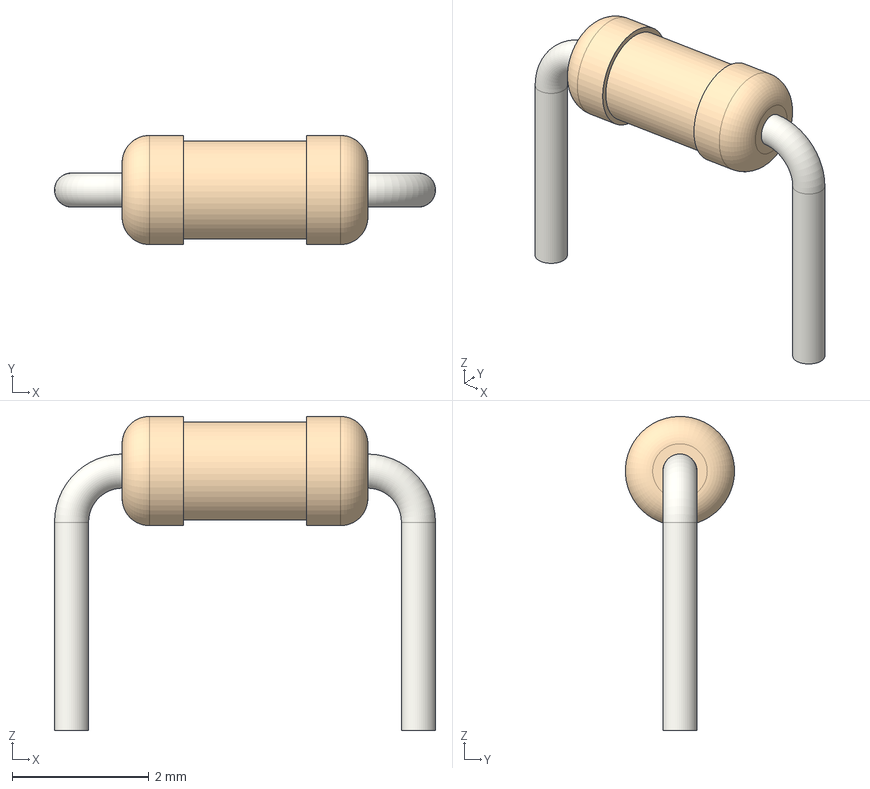
[picture p138: CAD file, 2023-04-15]
eda/future_badge/3d_models/R_Axial_DIN0204_L3.6mm_D1.6mm_P5.08mm_Horizontal.step
5.58 x 1.60 x 4.60 mm
