gowenrw/future_badge/eda/future_badge/3d_models/LED_D3.0mm.step

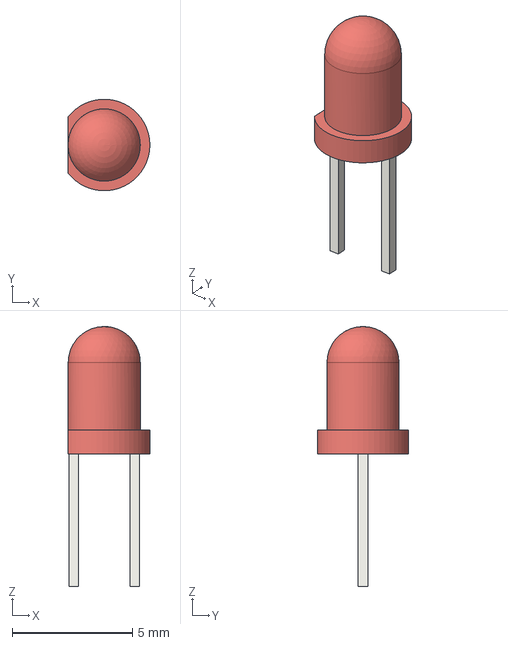
[picture p139: CAD file, 2023-04-15]
eda/future_badge/3d_models/LED_D3.0mm.step
3.40 x 3.80 x 10.8 mm
