gowenrw/future_badge/eda/future_badge/3d_models/SW_PUSH_6mm.step

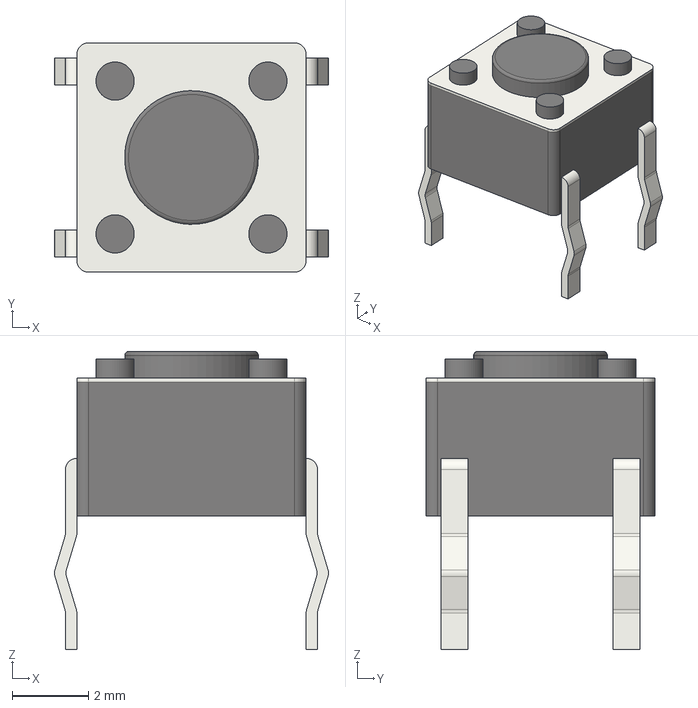
[picture p140: CAD file, 2023-04-15]
eda/future_badge/3d_models/SW_PUSH_6mm.step
7.17 x 6.00 x 7.80 mm
