gowenrw/future_badge/eda/future_badge/3d_models/C_Disc_D3.0mm_W2.0mm_P2.50mm.step

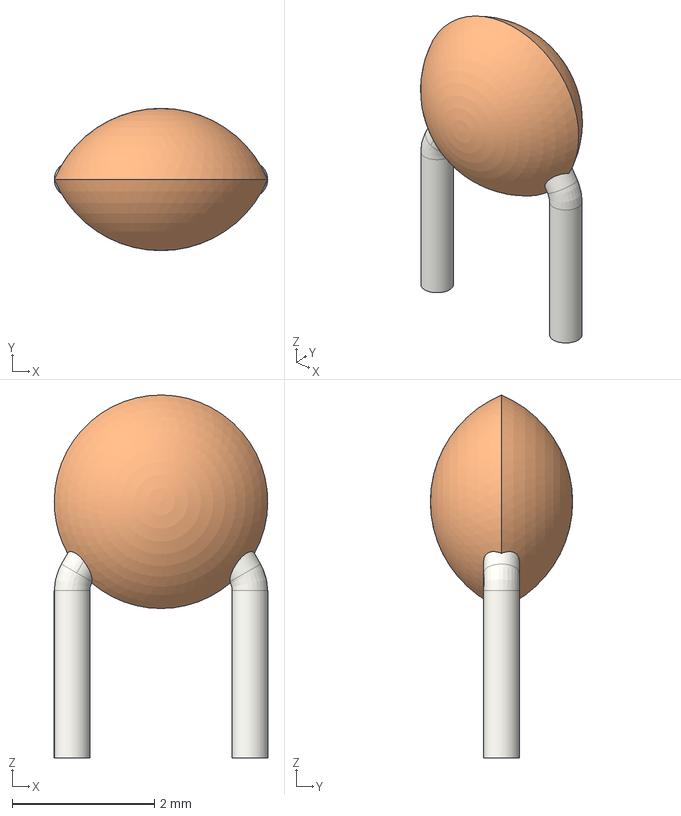
[picture p145: CAD file, 2023-04-15]
eda/future_badge/3d_models/C_Disc_D3.0mm_W2.0mm_P2.50mm.step
3.00 x 2.00 x 5.10 mm
