gowenrw/future_badge/eda/future_badge/3d_models/PinHeader_1x08_P2.54mm_Vertical.step

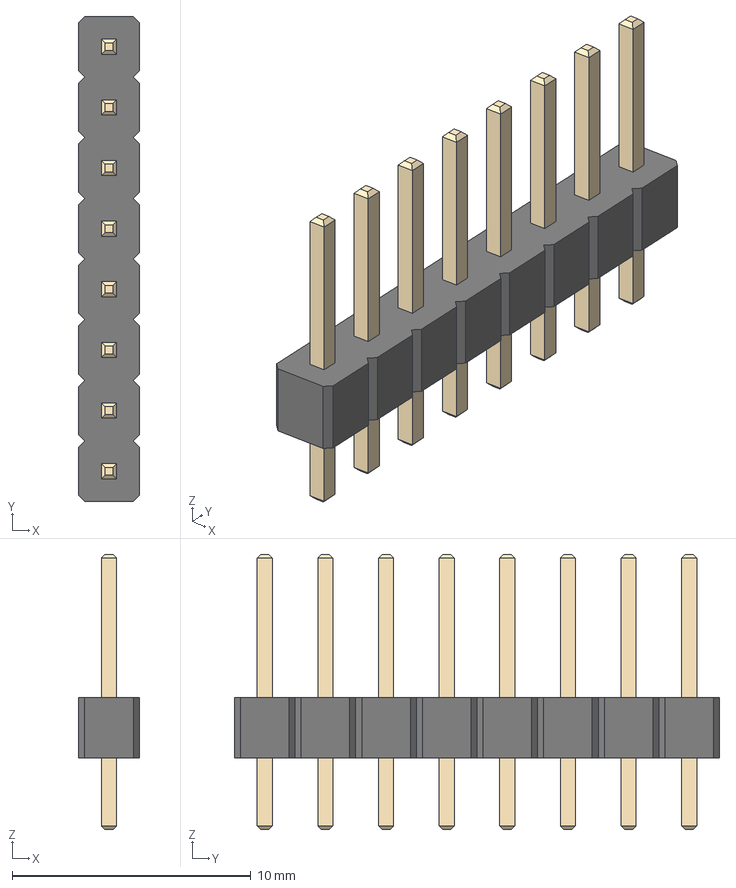
[picture p146: CAD file, 2023-04-15]
eda/future_badge/3d_models/PinHeader_1x08_P2.54mm_Vertical.step
2.54 x 20.3 x 11.5 mm
