gowenrw/future_badge/art/prototype_pcb_assembled.jpg

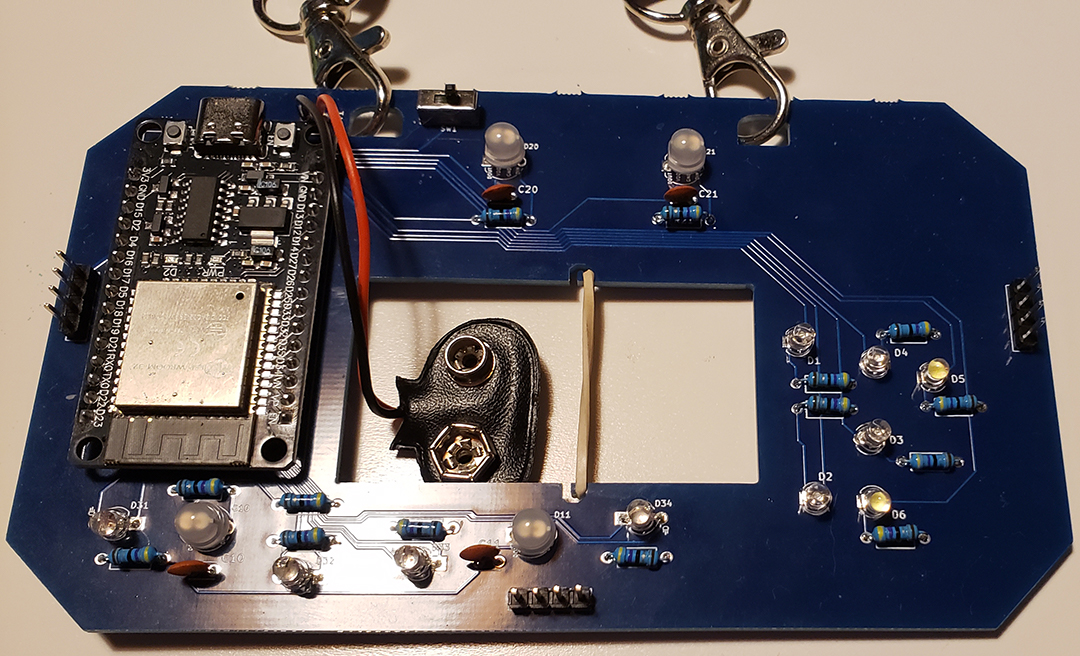
art/prototype_pcb_assembled.jpg
